OPad-dev/OPad/hardware/pcb/V1/HE/production/aisler/he_input_v1-schematic.pdf

1 | 2 | 3 | 4 | 5 | 6
1 | 2 | 3 | 4 | 5 | 6

AB

C

D

AB

C

### D Date: 2026-10-10

Size: A4 | Rev: V1.1
KiCad E.D.A. 10.0.6 | Id: 1/1

## Title: osuPad Hall Effect Input Module V1

### File: he_input_v1.kicad_sch

### Sheet: /

osuPad

PWR_FLAG

C2
100nF
VCC 1 | OUT | 2 GND 3 | U1 DRV5055A3
VCC 1 | OUT | 2 GND 3 | U2 DRV5055A3

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
J1 MODULE | C3

100nF

TP1

IO6

TP3

IO2 | R1
100k R2
47k | PWR_FLAG

C1

100nF 3V3 3V3

3V3 | 3V3
3V3 GND | GND GND

GND

IN1

IN2 | GND ID ID 3V3 GND

ID
IO6 | 3V3IO2 IO4 | GND

GND

IO4

IO2 IO6

3V3

IN1

IN2 | GND U1/U2 output a ratiometric analog voltage centred on VCC/2; the firmware tracks the peak and applies the rapid-trigger threshold. Module ID: 3V3 x 47k / (100k + 47k) = 1.06 V, read on GPIO8 and decoded as "Hall Effect module V1". Everything is on the bottom side. U1 and U2 sit on the key centres over solid FR-4, with no copper pour in the magnetic path.
J1-6/7/8 are reserved for an SPI variant and are brought out to probe pads TP1..TP3 instead of being left floating. osuPad Hall Effect (Rapid Trigger) input module V1 - two DRV5055 linear Hall sensors Module connector pinout, identical on every osuPad input module: 1 3V3 | 2 GND | 3 IN1 = GPIO10 (ADC1_CH9) | 4 IN2 = GPIO7 (ADC1_CH6) | 5 ID = GPIO8 (ADC1_CH7) | 6 GPIO6 | 7 GPIO4 | 8 GPIO2
