OPad-dev/OPad/osupad_windows_support_plan.md

# osu!pad — Windows Support, Installer and Device Pairing

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

---

## 0. Scope and decisions

### Goal

Ship osu!pad on Windows 10/11 with a real installer, and make the pad and the app feel like **one product** without ever locking the user out of their own hardware.

### Decided (owner, 2026-09-16)

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

### Open decision

- **Version number.** `v1.0.0` is already tagged and published. This plan assumes Windows ships as **`v1.1.0`**; re-cutting a published tag is not recommended. Owner to confirm.

### The one invariant that overrides everything

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

### What "vendor lock, but not really a lock" means here

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

---

## 1. What already works on Windows (verify, don't rewrite)

Confirmed by reading the tree at `0a5c13e`:

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

---

## 2. W0: make the workspace build on Windows (do these first)

Nothing else can be tested until `cargo build --target x86_64-pc-windows-msvc` succeeds.

### W0-1. Abstract the IPC transport

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

---

### W0-2. IPC hardening on Windows (the P2-6 equivalent)

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

---

### W0-3. Single-instance guard for the GUI

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

---

### W0-4. Storage and config paths

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

---

### W0-5. Cross-platform tray

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

---

### W0-6. Resolve the remaining `cfg(target_os = "linux")` sites

**Where.** `desktop/gui/src/main.rs:5, 278, 706, 743, 1008, 1734`

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

---

## 3. W1: Windows platform integration

### W1-1. `platform_windows.rs`

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

---

### W1-2. Hotplug detection

**Problem.** The Linux daemon relies on udev (`packaging/linux/udev/99-osupad.rules`) plus reconnect polling. Windows has no udev.

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

---

### W1-3. Flashing on Windows

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

**Acceptance.** Recovery flash works on Windows with the GUI running, without manually stopping the daemon first.

---

## 4. W2: Installer and uninstaller

### W2-1. Inno Setup script

**Where.** New `packaging/windows/osupad.iss`, plus a build script alongside `scripts/release`.

**Installs:**
- `osupad-gui.exe`, `osupad-daemon.exe`, `osupad-cli.exe` → `%LOCALAPPDATA%\Programs\osupad\`

  Per-user install, not `Program Files`. This avoids requiring admin rights, matches the per-user daemon model, and keeps the uninstall entirely inside the user's own profile.
- Start Menu shortcut for the GUI. **No desktop shortcut by default** — offer it as an unchecked checkbox.
- The `HKCU\...\Run` autostart value from W1-1, as an opt-in checkbox on the final page ("Start osu!pad when I log in", default checked).
- Uninstall entry under `HKCU\Software\Microsoft\Windows\CurrentVersion\Uninstall\osupad`.

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

---

### W2-2. Code signing

Unsigned installers trigger SmartScreen ("Windows protected your PC"), which for a keyboard-adjacent download is a real adoption problem — users are right to be suspicious of unsigned software that installs a keyboard tool at login.

**Options, owner's call:**
- Sign with an OV/EV certificate (~$200-400/yr; EV clears SmartScreen immediately, OV builds reputation over time).
- Ship unsigned and document the SmartScreen bypass in the README.

Not a blocker for a first release; it is a blocker for a comfortable one. Flagging it now so it is a decision, not a surprise.

---

### W2-3. Strong uninstall — no garbage left

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

  > "Also delete your osu!pad settings and lifetime key counters? This cannot be undone."

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

**Acceptance.** Install → use → uninstall (choosing "delete everything") leaves **zero** osu!pad files and **zero** registry values. Verify with a filesystem+registry diff across the whole cycle, and record the procedure in `docs/testing-checklist.md` as a new section. Run the same check for the "keep my data" path and confirm that `%APPDATA%\osupad\` is the *only* thing left.

---

## 5. W3: Device pairing / ownership claim

Cross-platform — this ships on Linux too, not just Windows.

### W3-1. Install identity

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

---

### W3-2. Firmware: owner field in NVS

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

---

### W3-3. Daemon and GUI: the takeover prompt

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

> "This osu!pad is paired with another installation. Its lifetime counters are 1,234,567 / 1,234,567.
> **[Take over and keep the pad's counters]** · [Take over and use this PC's counters] · [Leave it alone]"

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

---

### W3-4. Documented reflash (the nuke path)

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

---

## 6. W4: Verification and release

### W4-1. CI

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

### W4-2. Windows hardware checklist

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

Add a new section for W2-3's install/uninstall filesystem+registry diff.

### W4-3. Latency on Windows

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

### W4-4. Docs

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

---

## 7. Order of work

```
W0-1 ─┬─ W0-2                     (IPC: everything blocks on this)
      └─ W0-3
W0-4, W0-5, W0-6                  (parallel, independent)
   ↓
W1-1, W1-2, W1-3                  (platform integration)
   ↓
W2-1 ─ W2-3                       (installer; W2-2 signing is a side decision)
   ↓
W3-1 → W3-2 → W3-3 → W3-4         (pairing; cross-platform, ships on Linux too)
   ↓
W4-1 … W4-4
```

W3 (pairing) is independent of W0-W2 and could be done first on Linux if Windows stalls. W0-1 blocks every other Windows task and should be the first commit.

---

## 8. Risks

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

---

## 9. Out of scope

- macOS.
- MSIX packaging and Store-style "plug in the pad → Windows offers the app". That needs a Store-signed MSIX; the Inno decision rules it out. The daemon-at-login plus hotplug detection (W1-2) delivers nearly the same feel.
- Any cryptographic enforcement of the pairing model (§0).
- Windows Service hosting for the daemon (W1-1).
- v2 rapid trigger — see `osupad_v2_rapid_trigger_plan.md`.
