OPad-dev/OPad/hardware/pcb/V1/MX/production/mx_input_v1-bottom.png

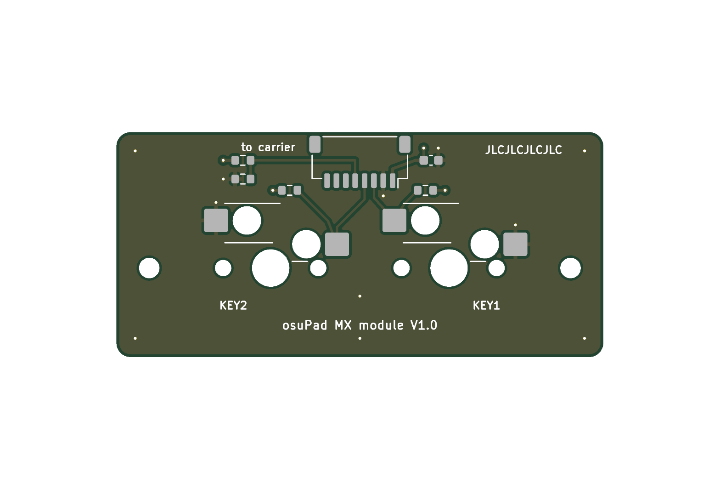
hardware/pcb/V1/MX/production/mx_input_v1-bottom.png
