OPad-dev/OPad/hardware/3d/custom_case/V1.1/tools/waveshare_back.scad

// Parts on the back of the Waveshare ESP32-S3-Touch-LCD-2 taller than 0.8 mm, as
// bounding boxes measured from Waveshare's STEP model (2024-11-08). Deck frame:
// [x0, x1, a0, a1, d0, d1], d = depth behind the glass front. The male headers
// and the four M2 standoffs are included; the model itself is not redistributed.
WS_BACK_BOXES = [
    [10.92, 12.52, 9.43, 12.43, 7.25, 8.35],
    [5.71, 6.53, 9.55, 9.85, 7.22, 8.04],
    [5.72, 6.52, 8.55, 9.55, 7.23, 8.03],
    [5.71, 6.53, 8.25, 8.55, 7.22, 8.04],
    [18.15, 25.20, -4.17, 4.17, 7.20, 10.15],
    [17.79, 18.66, 2.12, 2.39, 7.20, 8.64],
    [17.79, 18.66, -2.39, -2.13, 7.20, 8.64],
    [17.79, 18.66, 1.62, 1.87, 7.20, 8.64],
    [17.79, 18.66, -1.88, -1.63, 7.20, 8.64],
    [17.79, 24.37, 0.12, 0.38, 7.20, 9.22],
    [17.79, 24.37, -0.38, -0.12, 7.20, 9.22],
    [17.79, 24.37, 0.62, 0.88, 7.20, 8.76],
    [17.79, 24.38, -0.88, -0.62, 7.20, 8.76],
    [18.66, 24.37, -0.38, -0.12, 8.52, 8.76],
    [18.66, 24.37, 0.12, 0.38, 8.52, 8.76],
    [17.79, 24.93, -3.43, -2.57, 7.20, 8.78],
    [17.79, 24.58, -1.43, -1.07, 7.20, 9.22],
    [18.66, 24.58, -1.43, -1.07, 8.52, 8.76],
    [17.79, 24.57, 1.07, 1.43, 7.20, 9.22],
    [18.66, 24.58, 1.07, 1.43, 8.52, 8.76],
    [17.79, 24.92, 2.57, 3.43, 7.20, 8.78],
    [20.16, 24.37, 0.63, 0.88, 8.98, 9.22],
    [20.16, 24.38, -0.87, -0.62, 8.98, 9.22],
    [17.79, 24.93, -3.53, -2.41, 7.20, 9.22],
    [17.79, 24.93, 2.41, 3.53, 7.20, 9.22],
    [17.97, 25.50, -4.79, 4.79, 7.20, 10.45],
    [-16.58, -13.58, -5.26, -2.26, 7.20, 8.50],
    [1.15, 3.65, 3.46, 7.96, 7.21, 8.71],
    [1.15, 3.65, 8.09, 12.59, 7.21, 8.71],
    [17.55, 17.85, -12.62, -11.80, 7.22, 8.04],
    [16.55, 17.55, -12.61, -11.81, 7.23, 8.03],
    [16.25, 16.55, -12.62, -11.80, 7.22, 8.04],
    [11.48, 13.78, -11.96, -9.53, 7.20, 8.20],
    [15.18, 18.18, 9.15, 12.15, 7.20, 8.50],
    [-0.72, 2.48, -1.33, 1.32, 7.30, 8.06],
    [1.98, 2.18, 0.92, 1.12, 7.50, 8.08],
    [-8.49, -3.84, 2.85, 3.55, 7.25, 9.50],
    [-8.49, -3.84, -1.55, -0.85, 7.25, 9.50],
    [-8.49, -3.84, -0.45, 0.25, 7.25, 9.50],
    [-8.49, -3.84, -4.85, -4.15, 7.25, 9.50],
    [-8.49, -3.84, -3.75, -3.05, 7.25, 9.50],
    [-8.49, -3.84, -2.65, -1.95, 7.25, 9.50],
    [-8.49, -3.39, 3.78, 4.55, 7.25, 9.50],
    [-8.49, -3.84, 1.75, 2.45, 7.25, 9.50],
    [-8.49, -3.84, 0.65, 1.35, 7.25, 9.50],
    [-7.72, -3.19, 4.70, 5.35, 7.25, 9.20],
    [-8.49, -3.89, -6.05, 5.35, 7.30, 9.67],
    [-8.49, -2.99, -6.05, 5.35, 7.25, 9.90],
    [7.27, 9.57, 9.72, 12.16, 7.20, 8.20],
    [-17.55, 17.97, 13.97, 16.51, 7.20, 15.50],
    [-17.55, 17.97, -16.51, -13.97, 7.20, 15.50],
    [20.38, 24.04, 7.19, 11.75, 7.20, 9.00],
    [20.36, 24.02, -11.73, -7.17, 7.20, 9.00],
    [19.56, 23.06, 12.75, 16.25, 7.20, 9.71],
    [19.56, 23.06, -16.25, -12.75, 7.20, 9.71],
    [-22.64, -19.14, -16.25, -12.75, 7.20, 9.71],
    [-22.64, -19.14, 12.75, 16.25, 7.20, 9.71],
    [1.21, 6.41, -12.92, -5.27, 7.20, 10.60],
    [8.14, 13.83, -8.60, 8.60, 7.20, 9.20],
    [-7.28, -2.11, 6.95, 12.12, 7.20, 9.00],
    [-17.97, -10.27, 3.35, 11.42, 7.20, 8.20],
    [-23.49, -21.49, -8.50, -1.50, 7.20, 8.20]
];
