OPad-dev/OPad/desktop/daemon/src/main.rs

#![cfg_attr(windows, windows_subsystem = "windows")]

use anyhow::{Context, Result};
use parking_lot::Mutex;
use std::collections::HashMap;
use std::sync::atomic::{AtomicBool, Ordering};
use std::sync::Arc;
use std::time::{Duration, Instant};
use tracing::{error, info, warn};
use tracing_subscriber::layer::SubscriberExt;
use tracing_subscriber::util::SubscriberInitExt;

use opad_device::{DeviceEvent, DeviceManager};
use opad_ipc::{create_listener, get_socket_path};
use opad_layout::{Layout, Screen};
use opad_model::{CounterState, DeviceConfig, LogSource, RuntimeMode};
use opad_storage::Storage;
use opad_tosu::{spawn_tosu_supervisor, TosuManager};

pub mod backup;
pub mod device_actor;
pub mod firmware_update;
pub mod identity;
pub mod ipc_handlers;
pub mod log_hub;
pub mod osu_window;
pub mod runtime;
pub mod sync;
pub mod tap_stats;
pub mod telemetry;
pub mod updater;

use device_actor::DeviceCommand;
use log_hub::{LogHub, LogHubLayer};
use runtime::{apply_event, PendingOperations, RuntimeAction, RuntimeController, RuntimeEvent};
use sync::perform_sync;

#[tokio::main]
async fn main() -> Result<()> {
    let log_hub = LogHub::new();
    let fmt_layer = tracing_subscriber::fmt::layer();
    let hub_layer = LogHubLayer::new(log_hub.clone());
    let filter = tracing_subscriber::EnvFilter::from_default_env()
        .add_directive(tracing::Level::INFO.into());

    tracing_subscriber::registry()
        .with(filter)
        .with(fmt_layer)
        .with(hub_layer)
        .init();

    // A panic in any task takes the whole daemon down, loudly, so the service
    // manager (systemd Restart=on-failure) restarts it clean. Left alone, tokio
    // swallows a task's panic and the daemon limps on with that task missing.
    std::panic::set_hook(Box::new(|info| {
        let backtrace = std::backtrace::Backtrace::force_capture();
        error!("opad-daemon panicked: {}\n{}", info, backtrace);
        eprintln!("opad-daemon panicked: {info}");
        std::process::exit(1);
    }));

    info!("Starting opad-daemon v{}", env!("CARGO_PKG_VERSION"));

    let socket_path = get_socket_path();
    if opad_ipc::connect(&socket_path).await.is_ok() {
        anyhow::bail!(
            "Another opad-daemon instance is already running at {}",
            socket_path.display()
        );
    }

    let db_path = opad_model::paths::database_path()
        .context("Cannot resolve where to keep the OPad database")?;
    info!("Using SQLite database at {}", db_path.display());
    let (
        storage,
        storage_error,
        initial_config,
        initial_device,
        initial_counters,
        initial_layouts,
        existing_ids,
    ) = match Storage::open(&db_path) {
        Ok(s) => {
            let cfg = s.load_config().unwrap_or_default();
            let latest = s.load_latest_device_state().unwrap_or(None);
            let mut layouts = HashMap::new();
            for screen in Screen::ALL {
                if let Ok(Some(json)) = s.load_layout(screen.to_wire()) {
                    if let Ok(layout) = Layout::from_json(&json) {
                        layouts.insert(*screen, layout);
                    }
                }
            }
            let (init_dev, init_cnt) = match latest {
                Some((info, counters)) => (Some(info), counters),
                None => (None, CounterState::default()),
            };
            let existing = s
                .list_device_states()
                .unwrap_or_default()
                .into_iter()
                .map(|(info, _)| info.device_id)
                .collect();
            info!("opad-daemon initialized, storage loaded successfully");
            (
                Arc::new(Mutex::new(Some(s))),
                None,
                cfg,
                init_dev,
                init_cnt,
                layouts,
                existing,
            )
        }
        Err(e) => {
            let err_msg = format!("Database error ({}): {}", db_path.display(), e);
            error!(
                "Failed to open/migrate SQLite database: {}. Starting in degraded mode (§P2-12)",
                err_msg
            );
            (
                Arc::new(Mutex::new(None)),
                Some(err_msg),
                DeviceConfig::default(),
                None,
                CounterState::default(),
                HashMap::new(),
                Vec::new(),
            )
        }
    };

    // This install's identity (§W3-1), needed before the first pad connects
    // so an unclaimed pad can be claimed silently on that first HelloAck.
    let install_id = identity::load_or_create(&storage);
    if install_id.is_none() {
        warn!("Running with no install identity; pad ownership will not be recorded (§W3-1)");
    }

    let start_now = Instant::now();
    let mut controller = RuntimeController::new(
        initial_config.clone(),
        initial_device,
        initial_counters,
        initial_layouts,
        storage_error,
        existing_ids,
        start_now,
    );

    controller.set_install_id(install_id.clone());

    // Seed the last-backup time from the directory so a restart reports what
    // is really there rather than "Never".
    match backup::backup_dir() {
        Ok(dir) => {
            controller.state.last_backup = backup::newest(&dir).map(backup::format_stamp);
            info!(
                "Automatic counter backups: {} (keeping the {} most recent, written {:?} after a session settles)",
                dir.display(),
                backup::KEEP,
                runtime::AUTO_BACKUP_DELAY
            );
        }
        Err(e) => warn!("Automatic counter backups are unavailable: {}", e),
    }

    // Tap rate statistics (issue #2): the configured period and its history
    if let Some(s) = storage.lock().as_ref() {
        let tap = &mut controller.state.tap.snapshot;
        match s.tap_history_days() {
            Ok(days) => tap.period_days = days,
            Err(e) => warn!("Cannot read the tap rate history period: {}", e),
        }
        match s.tap_history(tap.period_days, chrono::Utc::now()) {
            Ok(history) => tap.history = Some(history),
            Err(e) => warn!("Cannot read the tap rate history: {}", e),
        }
    }

    let daemon_state = Arc::new(Mutex::new(controller.state.clone()));
    let pending_ops = Arc::new(Mutex::new(PendingOperations::default()));

    // Launch and supervise tosu, then follow its WebSocket
    let tosu_log_path =
        opad_model::paths::tosu_log_path().context("Cannot resolve where to keep the tosu log")?;

    if tosu_log_path.is_file() {
        if let Ok(content) = std::fs::read_to_string(&tosu_log_path) {
            let lines: Vec<&str> = content.lines().collect();
            let start = lines.len().saturating_sub(150);
            for line in &lines[start..] {
                let clean = opad_tosu::strip_ansi(line);
                let trimmed = clean.trim();
                if !trimmed.is_empty() {
                    log_hub.push(
                        LogSource::Tosu,
                        classify_tosu_line(trimmed),
                        "tosu",
                        trimmed,
                    );
                }
            }
        }
    }

    let lh = log_hub.clone();
    let tosu_cb = Arc::new(move |line: &str| {
        let clean = line.trim();
        if !clean.is_empty() {
            lh.push(LogSource::Tosu, classify_tosu_line(clean), "tosu", clean);
        }
    });

    let tosu_supervisor = spawn_tosu_supervisor(
        initial_config.tosu_endpoint.clone(),
        tosu_log_path,
        Some(tosu_cb),
    );
    let (tosu_manager, mut tosu_rx) = TosuManager::new(initial_config.tosu_endpoint.clone());
    let mut tosu_connected_rx = tosu_manager.subscribe_connected();
    let mut tosu_keys_rx = tosu_manager.subscribe_keys();
    tosu_manager.start();
    let mut osu_active_rx = osu_window::watch();

    // Start Device CDC manager
    let (device_manager, mut device_rx) = DeviceManager::new();
    let device_manager = Arc::new(device_manager);
    // Every runtime action reaches the pad through this one ordered queue
    let resend_data = Arc::new(AtomicBool::new(false));
    let device_cmd = device_actor::spawn(device_manager.clone(), resend_data.clone());

    // Setup Local IPC Server
    let socket_path = get_socket_path();
    let ipc_listener = match create_listener(&socket_path) {
        Ok(l) => l,
        Err(opad_ipc::IpcError::AlreadyRunning) => {
            eprintln!("opad-daemon is already running");
            std::process::exit(0);
        }
        Err(e) => return Err(e.into()),
    };

    // Updates: tosu (§U-1) and the app (§U-2). Idle-only, daily, and inert
    // until a signing key is compiled in (§U-0.3).
    let update_service =
        updater::spawn_update_worker(daemon_state.clone(), storage.clone(), tosu_supervisor);

    // Spawn IPC request handling task
    {
        let daemon_state = daemon_state.clone();
        let storage = storage.clone();
        let device_manager = device_manager.clone();
        let log_hub = log_hub.clone();
        let pending_ops = pending_ops.clone();
        let update_service = update_service.clone();

        tokio::spawn(async move {
            loop {
                match ipc_listener.accept().await {
                    Ok(mut stream) => {
                        let daemon_state = daemon_state.clone();
                        let storage = storage.clone();
                        let device_manager = device_manager.clone();
                        let log_hub = log_hub.clone();
                        let pending_ops = pending_ops.clone();
                        let update_service = update_service.clone();

                        tokio::spawn(async move {
                            ipc_handlers::serve_connection(
                                &mut stream,
                                &daemon_state,
                                &storage,
                                &*device_manager,
                                &log_hub,
                                &pending_ops,
                                Some(&update_service),
                            )
                            .await;
                        });
                    }
                    Err(e) => {
                        warn!("IPC accept error: {}", e);
                    }
                }
            }
        });
    }

    // Main Runtime Coordinator loop (§11: IDLE <-> PLAYING <-> COOLDOWN <-> SYNC)
    let mut tick = tokio::time::interval(Duration::from_millis(50));
    let mut last_db_retry = Instant::now();
    let mut last_instant = Instant::now();
    let mut last_system_time = std::time::SystemTime::now();
    // Syncs run in their own task (they can take ~10 s) and report back here
    let (sync_done_tx, mut sync_done_rx) =
        tokio::sync::mpsc::unbounded_channel::<Result<CounterState, String>>();

    loop {
        let mut event_opt = None;

        tokio::select! {
            // 1. Device hardware events
            res = device_rx.recv() => {
                let dev_event = match res {
                    Ok(ev) => ev,
                    Err(tokio::sync::broadcast::error::RecvError::Lagged(skipped)) => {
                        // Whatever was skipped (a Connected, a Counters) is
                        // lost; ask the pad to announce itself again
                        warn!("Fell {} device events behind; re-handshaking with the pad", skipped);
                        device_manager.rehandshake();
                        continue;
                    }
                    Err(tokio::sync::broadcast::error::RecvError::Closed) => {
                        anyhow::bail!("The device event channel closed");
                    }
                };
                match dev_event {
                    DeviceEvent::Connected(info, dev_cfg) => {
                        info!(
                            "ESP32 Device Connected: ID={}, Board={}, Firmware={}, Slot={}",
                            info.device_id,
                            info.board_profile,
                            info.firmware_version,
                            info.running_partition.as_deref().unwrap_or("unknown"),
                        );
                        event_opt = Some(RuntimeEvent::DeviceConnected(info, dev_cfg));
                    }
                    DeviceEvent::Ownership { owner_id } => {
                        event_opt = Some(RuntimeEvent::DeviceOwnership(owner_id));
                    }
                    DeviceEvent::Disconnected => {
                        warn!("ESP32 Device Disconnected");
                        event_opt = Some(RuntimeEvent::DeviceDisconnected);
                    }
                    DeviceEvent::Counters(c) => {
                        event_opt = Some(RuntimeEvent::DeviceCounters(c));
                    }
                    DeviceEvent::StatusUpdate(status) => {
                        event_opt = Some(RuntimeEvent::DeviceLatency(opad_model::LatencyStats {
                            samples: status.latency_samples,
                            p50_us: status.latency_p50_us,
                            p99_us: status.latency_p99_us,
                            p999_us: status.latency_p999_us,
                            max_us: status.latency_max_us,
                            deferred_reports: status.hid_deferred_reports,
                        }));
                    }
                    DeviceEvent::CounterSyncResult { .. } => {}
                    DeviceEvent::ConfigAck { .. } => {}
                    DeviceEvent::LayoutAck { screen, success, message } => {
                        let note = if message.is_empty() { String::new() } else { format!(" ({})", message) };
                        info!(
                            "Layout {} {}{}",
                            Screen::from_wire(screen).map_or("?", |s| s.label()),
                            if success { "applied" } else { "rejected" },
                            note
                        );
                        event_opt = Some(RuntimeEvent::DeviceLayoutAck { screen, success, message });
                    }
                    DeviceEvent::LogBatch(batch) => {
                        event_opt = Some(RuntimeEvent::DeviceLogBatch(batch));
                    }
                    DeviceEvent::PinDetected { .. } | DeviceEvent::BoardTest(_) => {}
                    DeviceEvent::KeyPressTimes(on) => {
                        event_opt = Some(RuntimeEvent::PadPressTimes(on));
                    }
                    DeviceEvent::KeyPresses { now_us, presses, dropped, received } => {
                        event_opt = Some(RuntimeEvent::PadPresses { now_us, presses, dropped, received });
                    }
                }
            }

            // 2. Telemetry events from tosu
            Ok(telemetry) = tosu_rx.recv() => {
                event_opt = Some(RuntimeEvent::TosuTelemetry {
                    is_playing: telemetry.is_playing,
                    live_time_ms: telemetry.live_time_ms,
                    title: telemetry.title,
                    values: telemetry.values,
                    beatmap: telemetry.beatmap,
                    failed: telemetry.failed,
                    clock: telemetry.clock,
                    other_player: telemetry.other_player,
                });
            }

            // 2b. osu!'s key counters, for the tap rate (issue #2). A lag
            //     loses a few presses from one attempt's statistics, nothing
            //     more, so it is not worth resynchronising anything for.
            res = tosu_keys_rx.recv() => {
                match res {
                    Ok(keys) => event_opt = Some(RuntimeEvent::TosuKeys(keys)),
                    Err(tokio::sync::broadcast::error::RecvError::Lagged(n)) => {
                        warn!("Fell {} tosu key updates behind; the tap rate skips them", n);
                    }
                    Err(tokio::sync::broadcast::error::RecvError::Closed) => {}
                }
            }

            // 3. tosu WebSocket connected / disconnected
            Ok(()) = tosu_connected_rx.changed() => {
                let connected = *tosu_connected_rx.borrow_and_update();
                info!("{}", if connected { "tosu connected" } else { "tosu disconnected" });
                event_opt = Some(RuntimeEvent::TosuConnectionChanged(connected));
            }

            // 3b. osu! came to the front / started, or went away: where the
            //     pad's volume swipes go
            Ok(()) = osu_active_rx.changed() => {
                let active = *osu_active_rx.borrow_and_update();
                info!("{}", if active { "osu! active: volume swipes go to osu!" } else { "osu! inactive: volume swipes set the system volume" });
                event_opt = Some(RuntimeEvent::OsuActiveChanged(active));
            }

            // 4. A background sync finished
            Some(res) = sync_done_rx.recv() => {
                event_opt = Some(match res {
                    Ok(counters) => RuntimeEvent::SyncCompleted {
                        success: true,
                        counters,
                        time_str: Some(chrono::Utc::now().to_rfc3339()),
                        error: None,
                    },
                    Err(e) => RuntimeEvent::SyncCompleted {
                        success: false,
                        // Unchanged by the failed sync; the shared state, not
                        // the controller's copy from the previous event
                        counters: daemon_state.lock().counters.clone(),
                        time_str: None,
                        error: Some(e),
                    },
                });
            }

            // 5. Periodic tick
            _ = tick.tick() => {
                let now = Instant::now();

                // Periodic clock jump check
                let now_system = std::time::SystemTime::now();
                let elapsed_instant = now.saturating_duration_since(last_instant);
                let clock_jump = match now_system.duration_since(last_system_time) {
                    Ok(sys_elapsed) => sys_elapsed.abs_diff(elapsed_instant) > Duration::from_secs(2),
                    Err(_) => true,
                };
                last_instant = now;
                last_system_time = now_system;

                if clock_jump && {
                    let ds = daemon_state.lock();
                    ds.device_connected && ds.mode == RuntimeMode::Idle
                } {
                    let _ = device_cmd.send(DeviceCommand::TimeSync).await;
                }

                // A telemetry diff met a full device queue, or a message to
                // the pad was lost on the wire: resend everything, or the
                // song, stars, ... stay missing until they next change
                let lost = device_manager.take_lost_writes();
                if resend_data.swap(false, Ordering::SeqCst) || lost {
                    controller.data_sync.reset_sent();
                }

                // Retry opening SQLite every 60s if unavailable (§P2-12)
                if storage.lock().is_none() && last_db_retry.elapsed() >= Duration::from_secs(60) {
                    last_db_retry = Instant::now();
                    info!("Retrying SQLite database connection at {}", db_path.display());
                    match Storage::open(&db_path) {
                        Ok(s) => {
                            info!("Successfully reconnected to SQLite database at {}", db_path.display());
                            let cfg = s.load_config().ok();
                            let mut layouts = Vec::new();
                            for screen in Screen::ALL {
                                if let Ok(Some(json)) = s.load_layout(screen.to_wire()) {
                                    if let Ok(l) = Layout::from_json(&json) {
                                        layouts.push((*screen, l));
                                    }
                                }
                            }
                            let device_id = daemon_state.lock().device_info.as_ref().map(|i| i.device_id.clone());
                            let stored_dev = if let Some(device_id) = &device_id {
                                s.load_device_state(device_id).unwrap_or(None)
                            } else {
                                None
                            };
                            *storage.lock() = Some(s);
                            let _ = apply_event(&mut controller, &daemon_state, &pending_ops, RuntimeEvent::SqliteReconnected {
                                config: cfg,
                                layouts,
                                stored_device: stored_dev,
                            }, now);
                        }
                        Err(e) => {
                            warn!("SQLite database reconnection attempt failed: {}", e);
                            let _ = apply_event(&mut controller, &daemon_state, &pending_ops, RuntimeEvent::SqliteError(format!("Database error ({}): {}", db_path.display(), e)), now);
                        }
                    }
                }

                event_opt = Some(RuntimeEvent::Tick(now));
            }
        }

        if let Some(event) = event_opt {
            let now = Instant::now();
            let actions = apply_event(&mut controller, &daemon_state, &pending_ops, event, now);

            for action in actions {
                match action {
                    RuntimeAction::SendTimeSync => {
                        let _ = device_cmd.send(DeviceCommand::TimeSync).await;
                    }
                    RuntimeAction::ClaimOwnership => {
                        // §W3-2: an NVS write, which the firmware honours only
                        // in IDLE. Connect time already is one.
                        if let Some(owner) =
                            install_id.as_deref().and_then(identity::parse_owner_id)
                        {
                            let _ = device_cmd
                                .send(DeviceCommand::ClaimOwnership(owner.to_vec()))
                                .await;
                        }
                    }
                    RuntimeAction::SendConfig(cfg) => {
                        let _ = device_cmd.send(DeviceCommand::Config(cfg)).await;
                    }
                    RuntimeAction::SaveDeviceConfig(cfg) => {
                        let s_guard = storage.lock();
                        if let Some(s) = s_guard.as_ref() {
                            if let Err(e) = s.save_config(&cfg) {
                                warn!("Failed to persist device configuration from pad: {}", e);
                            } else {
                                info!("Saved pad configuration to SQLite database");
                            }
                        }
                    }
                    RuntimeAction::SendHostStatus {
                        tosu_connected,
                        is_playing,
                        play_id,
                        osu_active,
                    } => {
                        let _ = device_cmd
                            .send(DeviceCommand::HostStatus {
                                tosu_connected,
                                is_playing,
                                play_id,
                                osu_active,
                            })
                            .await;
                    }
                    RuntimeAction::SendDataUpdate(changes) => {
                        let _ = device_cmd.send(DeviceCommand::DataUpdate(changes)).await;
                    }
                    RuntimeAction::SendLayout(screen, layout) => {
                        let _ = device_cmd.send(DeviceCommand::Layout(screen, layout)).await;
                    }
                    RuntimeAction::TakeOverIfPadIsAhead => {
                        let ds = daemon_state.clone();
                        let stg = storage.clone();
                        let dm = device_manager.clone();
                        let hub = log_hub.clone();
                        let po = pending_ops.clone();
                        tokio::spawn(async move {
                            ipc_handlers::take_over_if_pad_is_ahead(&ds, &stg, &*dm, &hub, &po)
                                .await;
                        });
                    }
                    RuntimeAction::TriggerSync => {
                        let ds = daemon_state.clone();
                        let stg = storage.clone();
                        let dm = device_manager.clone();
                        let po = pending_ops.clone();
                        let done = sync_done_tx.clone();
                        tokio::spawn(async move {
                            let res = perform_sync(&ds, &stg, &*dm, &po).await;
                            let _ = done.send(res);
                        });
                    }
                    RuntimeAction::RequestDeviceStatus => {
                        let _ = device_cmd.send(DeviceCommand::RequestStatus).await;
                    }
                    RuntimeAction::SetStorageWritesAllowed(allowed) => {
                        if let Some(s) = storage.lock().as_mut() {
                            s.set_writes_allowed(allowed);
                        }
                    }
                    RuntimeAction::SaveInitialDeviceState(info, counters) => {
                        if let Some(s) = storage.lock().as_ref() {
                            let _ = s.save_device_state(&info, &counters);
                        }
                    }
                    RuntimeAction::TouchDeviceLastSeen(device_id) => {
                        if let Some(s) = storage.lock().as_ref() {
                            let _ = s.touch_device_last_seen(&device_id);
                        }
                    }
                    RuntimeAction::PushEspLog {
                        level,
                        tag,
                        message,
                    } => {
                        log_hub.push(LogSource::Esp, level, &tag, message);
                    }
                    RuntimeAction::SaveTapStats {
                        attempts,
                        period_days,
                    } => {
                        // IDLE by construction. A failure keeps the attempts
                        // queued for the next IDLE tick rather than losing them.
                        let (unsaved, period_saved) = match storage.lock().as_ref() {
                            None => (Some(attempts), period_days.is_none()),
                            Some(s) => {
                                let unsaved = match s.save_tap_attempts(&attempts) {
                                    Ok(n) => {
                                        if n > 0 {
                                            info!("Saved the tap rate of {} attempts", n);
                                        }
                                        None
                                    }
                                    Err(e) => {
                                        warn!(
                                            "Cannot save the tap rate of {} attempts yet: {}",
                                            attempts.len(),
                                            e
                                        );
                                        Some(attempts)
                                    }
                                };
                                let period_saved = period_days.is_none_or(|days| {
                                    s.set_tap_history_days(days)
                                        .map_err(|e| {
                                            warn!(
                                                "Cannot save the tap rate history period yet: {}",
                                                e
                                            )
                                        })
                                        .is_ok()
                                });
                                (unsaved, period_saved)
                            }
                        };
                        if let Some(attempts) = unsaved {
                            controller.requeue_tap_attempts(attempts);
                        }
                        if !period_saved {
                            daemon_state.lock().tap.period_unsaved = true;
                        }
                        tap_stats::refresh_history(&storage, &daemon_state);
                    }
                    RuntimeAction::RefreshTapHistory => {
                        tap_stats::refresh_history(&storage, &daemon_state);
                    }
                    RuntimeAction::WriteAutoBackup => {
                        // Synchronous and cheap (one small JSON file), and we
                        // are in IDLE by construction. Every failure inside is
                        // logged and swallowed: a backup must never be able to
                        // take the daemon down or hold up anything else.
                        if let Some(backup) = backup::current(&daemon_state, &storage) {
                            if let Some(at) = backup::write_and_log(&backup) {
                                daemon_state.lock().last_backup = Some(backup::format_stamp(at));
                            }
                        }
                    }
                }
            }
        }
    }
}

/// Level of a tosu output line (ANSI already stripped), from its wording
fn classify_tosu_line(line: &str) -> opad_model::LogLevel {
    if line.contains("error") || line.contains("Error") {
        opad_model::LogLevel::Error
    } else if line.contains("warn") || line.contains("Warn") {
        opad_model::LogLevel::Warn
    } else {
        opad_model::LogLevel::Info
    }
}

#[cfg(test)]
mod tests {
    use super::*;

    #[test]
    fn tosu_lines_are_classified_by_their_wording() {
        use opad_model::LogLevel;
        assert_eq!(
            classify_tosu_line("[tosu] Error: port in use"),
            LogLevel::Error
        );
        assert_eq!(classify_tosu_line("socket error"), LogLevel::Error);
        assert_eq!(classify_tosu_line("Warn: slow memory read"), LogLevel::Warn);
        assert_eq!(classify_tosu_line("Server started"), LogLevel::Info);
    }

    use crate::ipc_handlers::handle_ipc_request;
    use crate::runtime::DaemonState;
    use opad_ipc::{IpcRequest, IpcResponse};
    use opad_model::{CounterSource, DeviceInfo};

    #[tokio::test]
    async fn test_sqlite_failure_isolation() {
        let (device_manager, _) = DeviceManager::new_dummy();
        let device_manager = Arc::new(device_manager);
        let log_hub = LogHub::new();
        let pending_ops = Arc::new(Mutex::new(PendingOperations::default()));
        let storage: Arc<Mutex<Option<Storage>>> = Arc::new(Mutex::new(None));

        let daemon_state = Arc::new(Mutex::new(DaemonState {
            mode: RuntimeMode::Idle,
            device_connected: true,
            device_info: Some(DeviceInfo {
                device_id: "OSUPAD-TEST".to_string(),
                board_profile: "waveshare_esp32s3_touch_lcd_2".to_string(),
                firmware_version: "1.0.0".to_string(),
                protocol_version: 1,
                running_partition: None,
            }),
            counters: CounterState {
                device_id: "OSUPAD-TEST".to_string(),
                counter_generation: 1,
                lifetime_key1: 50,
                lifetime_key2: 60,
                map_key1: 0,
                map_key2: 0,
            },
            counters_source: CounterSource::Device,
            pc_counters: None,
            esp_counters: Some(CounterState {
                device_id: "OSUPAD-TEST".to_string(),
                counter_generation: 1,
                lifetime_key1: 50,
                lifetime_key2: 60,
                map_key1: 0,
                map_key2: 0,
            }),
            config: DeviceConfig::default(),
            last_sync_time: None,
            last_sync_error: None,
            storage_error: Some("Database permission denied".to_string()),
            tosu_connected: false,
            osu_active: false,
            latency: None,
            pending_replacement: None,
            install_id: None,
            pending_takeover: None,
            foreign_pad: false,
            nvs_restore_pending: false,
            tap: Default::default(),
            incompatible: None,
            ui_values: Vec::new(),
            custom_layouts: HashMap::new(),
            last_backup: None,
        }));

        // 1. GetStatus surfaces storage_error
        let resp = handle_ipc_request(
            IpcRequest::GetStatus,
            &daemon_state,
            &storage,
            &*device_manager,
            &log_hub,
            &pending_ops,
            None,
        )
        .await;
        match resp {
            IpcResponse::Status { storage_error, .. } => {
                assert_eq!(
                    storage_error,
                    Some("Database permission denied".to_string())
                );
            }
            other => panic!("Expected Status response, got {:?}", other),
        }

        // 2. Destructive/reconciliation operations rejected without SQLite
        let resp = handle_ipc_request(
            IpcRequest::ForceSync,
            &daemon_state,
            &storage,
            &*device_manager,
            &log_hub,
            &pending_ops,
            None,
        )
        .await;
        assert!(matches!(resp, IpcResponse::OperationRejected { .. }));

        let resp = handle_ipc_request(
            IpcRequest::ResetCounters { confirm: true },
            &daemon_state,
            &storage,
            &*device_manager,
            &log_hub,
            &pending_ops,
            None,
        )
        .await;
        assert!(matches!(resp, IpcResponse::OperationRejected { .. }));

        let resp = handle_ipc_request(
            IpcRequest::RestoreDeviceFromPc { confirm: true },
            &daemon_state,
            &storage,
            &*device_manager,
            &log_hub,
            &pending_ops,
            None,
        )
        .await;
        assert!(matches!(resp, IpcResponse::OperationRejected { .. }));

        let resp = handle_ipc_request(
            IpcRequest::ImportPcFromDevice { confirm: true },
            &daemon_state,
            &storage,
            &*device_manager,
            &log_hub,
            &pending_ops,
            None,
        )
        .await;
        assert!(matches!(resp, IpcResponse::OperationRejected { .. }));

        // 3. Layouts still work in-memory
        let resp = handle_ipc_request(
            IpcRequest::GetLayouts,
            &daemon_state,
            &storage,
            &*device_manager,
            &log_hub,
            &pending_ops,
            None,
        )
        .await;
        assert!(matches!(
            resp,
            IpcResponse::Layouts {
                idle: None,
                playing: None
            }
        ));

        // 4. perform_sync does not modify ESP counters when storage is None
        let res = perform_sync(&daemon_state, &storage, &*device_manager, &pending_ops).await;
        assert!(res.is_err());
        let st = daemon_state.lock();
        assert_eq!(st.counters.lifetime_key1, 50);
        assert_eq!(st.counters.lifetime_key2, 60);
        assert!(st.last_sync_error.is_some());
    }
}
