OPad-dev/OPad/firmware/main/input/keypad.c

#include "keypad.h"
#include "debounce.h"
#include "boards/waveshare_esp32s3_touch_lcd_2/board.h"
#include "ui/ui.h"
#include "usb/usb_hid.h"
#include "freertos/FreeRTOS.h"
#include "freertos/task.h"
#include "esp_timer.h"
#include "esp_log.h"
#include <stdatomic.h>
#include "input/latency_stats.h"
#include "input/press_log.h"
#include "driver/gpio.h"
#include "esp_rom_sys.h"
#include "diag/diag.h"
#include "config/device_config.h"

static const char *TAG = "keypad";

static portMUX_TYPE s_keypad_spinlock = portMUX_INITIALIZER_UNLOCKED;
static debounce_state_t s_key_debounce[KEY_ID_COUNT];

#define KEYPAD_DEFAULT_KEY1_GPIO 14
#define KEYPAD_DEFAULT_KEY2_GPIO 9

static keypad_config_t s_config = {
    .keycode1 = 0x1D,       // 'z'
    .keycode2 = 0x1B,       // 'x'
    .debounce_us = DEBOUNCE_DEFAULT_US,
    .key1_gpio = KEYPAD_DEFAULT_KEY1_GPIO,
    .key2_gpio = KEYPAD_DEFAULT_KEY2_GPIO,
};

static keypad_config_t s_staged_config;
static volatile bool s_config_staged = false;

// Pin detection requests, served by the keypad task (the one task that may
// touch key GPIOs). Guarded by s_keypad_spinlock.
static uint32_t s_detect_req_id = 0;
static uint32_t s_detect_req_timeout_ms;
static uint32_t s_detect_req_exclude;
static uint32_t s_detect_done_id = 0;
static int s_detect_done_pin = -1;

// Key line test requests (keypad_line_test), also served by the keypad task.
// Guarded by s_keypad_spinlock.
static uint32_t s_line_test_req_id = 0;
static uint32_t s_line_test_done_id = 0;
static keypad_line_test_t s_line_test_result;

static volatile bool s_key_state[KEY_ID_COUNT] = {false, false};
static volatile int64_t s_last_transition_us[KEY_ID_COUNT] = {0, 0};
static atomic_llong s_key1_last_press_us = 0;
static atomic_llong s_key2_last_press_us = 0;

static atomic_uint_least64_t s_key1_lifetime_presses = 0;
static atomic_uint_least64_t s_key2_lifetime_presses = 0;
// Presses in the current osu! attempt; zeroed by the host on every new play
static atomic_uint_least32_t s_key1_map_presses = 0;
static atomic_uint_least32_t s_key2_map_presses = 0;

static TaskHandle_t s_input_task_handle = NULL;
// Off when the input module is one v1 cannot read (Hall Effect): its analog
// outputs on the key pins would otherwise register as presses
static volatile bool s_input_enabled = true;
static keypad_state_callback_t s_callback = NULL;

static void IRAM_ATTR gpio_isr_handler(void *arg)
{
    int key_index = (intptr_t)arg - 1;
    if (key_index < 0 || key_index >= KEY_ID_COUNT || !s_input_enabled) {
        return;
    }

    int64_t now = esp_timer_get_time();
    bool current_pressed = (key_index == 0) ? board_key1_read() : board_key2_read();

    portENTER_CRITICAL_ISR(&s_keypad_spinlock);
    debounce_action_t action = debounce_step(
        &s_key_debounce[key_index],
        now,
        current_pressed,
        DEBOUNCE_SOURCE_EDGE,
        s_config.debounce_us
    );

    if (action != DEBOUNCE_ACTION_NONE) {
        s_key_state[key_index] = s_key_debounce[key_index].accepted_pressed;
        s_last_transition_us[key_index] = s_key_debounce[key_index].last_transition_us;

        // Counting rule: only accepted press transitions increment counters.
        if (action == DEBOUNCE_ACTION_PRESS) {
            if (key_index == 0) {
                atomic_fetch_add_explicit(&s_key1_lifetime_presses, 1, memory_order_relaxed);
                atomic_fetch_add_explicit(&s_key1_map_presses, 1, memory_order_relaxed);
                atomic_store_explicit(&s_key1_last_press_us, now, memory_order_relaxed);
                press_log_push(1, now);
            } else {
                atomic_fetch_add_explicit(&s_key2_lifetime_presses, 1, memory_order_relaxed);
                atomic_fetch_add_explicit(&s_key2_map_presses, 1, memory_order_relaxed);
                atomic_store_explicit(&s_key2_last_press_us, now, memory_order_relaxed);
                press_log_push(2, now);
            }
        }

        BaseType_t high_task_wakeup = pdFALSE;
        if (s_input_task_handle != NULL) {
            vTaskNotifyGiveFromISR(s_input_task_handle, &high_task_wakeup);
            if (high_task_wakeup) {
                portYIELD_FROM_ISR();
            }
        }
    }
    portEXIT_CRITICAL_ISR(&s_keypad_spinlock);
}

// Pin level as a pressed state, or released while input is off: an HE module's
// analog outputs read as pressed and would hold a key down forever
static bool read_key_level(int key_index)
{
    if (!s_input_enabled) {
        return false;
    }
    return key_index == 0 ? board_key1_read() : board_key2_read();
}

// Start debouncing again from the pins as they read now. True if a key reads
// pressed, so the caller can have the keypad task report it.
static bool restart_debounce_from_pins(void)
{
    bool levels[KEY_ID_COUNT] = {read_key_level(0), read_key_level(1)};
    portENTER_CRITICAL(&s_keypad_spinlock);
    for (int i = 0; i < KEY_ID_COUNT; i++) {
        debounce_init(&s_key_debounce[i], levels[i]);
        s_key_state[i] = levels[i];
        s_last_transition_us[i] = esp_timer_get_time();
    }
    portEXIT_CRITICAL(&s_keypad_spinlock);
    return levels[0] || levels[1];
}

// How long a key line gets to settle after its pull changes. The pin, carrier
// trace and cable are tens of pF against a ~45k internal pull: microseconds.
#define LINE_TEST_SETTLE_US 300

/*
 * Swap each key pin's internal pull-up for a pull-down and read it. A line
 * that still reads high has an external pull-up: the MX module's 10k (R1/R2),
 * which proves the cable, the carrier trace and both connectors carry it. A
 * line low even with the pull-up is a held switch or a short to GND.
 *
 * Runs on the keypad task, about 1 ms. Edges are ignored meanwhile (no HID
 * report is sent in between, the task is busy here) and debouncing restarts
 * from the pins afterwards, so a key held through the test stays held.
 */
static void line_test_run(keypad_line_test_t *r)
{
    portENTER_CRITICAL(&s_keypad_spinlock);
    keypad_config_t cfg = s_config;
    portEXIT_CRITICAL(&s_keypad_spinlock);

    gpio_num_t pins[KEY_ID_COUNT] = {(gpio_num_t)cfg.key1_gpio, (gpio_num_t)cfg.key2_gpio};
    *r = (keypad_line_test_t){
        .gpio = {cfg.key1_gpio, cfg.key2_gpio},
    };
    if (!s_input_enabled) {
        return; // Hall Effect outputs on the pins: nothing a pull test can say
    }

    s_input_enabled = false;
    for (int i = 0; i < KEY_ID_COUNT; i++) {
        r->high_with_pullup[i] = gpio_get_level(pins[i]) != 0;
        gpio_set_pull_mode(pins[i], GPIO_PULLDOWN_ONLY);
    }
    esp_rom_delay_us(LINE_TEST_SETTLE_US);
    for (int i = 0; i < KEY_ID_COUNT; i++) {
        r->high_with_pulldown[i] = gpio_get_level(pins[i]) != 0;
        gpio_set_pull_mode(pins[i], GPIO_PULLUP_ONLY);
    }
    esp_rom_delay_us(LINE_TEST_SETTLE_US);
    s_input_enabled = true;
    restart_debounce_from_pins();
    r->ran = true;
}

static void line_test_step(void)
{
    portENTER_CRITICAL(&s_keypad_spinlock);
    uint32_t req_id = s_line_test_req_id;
    bool pending = req_id != s_line_test_done_id;
    portEXIT_CRITICAL(&s_keypad_spinlock);
    if (!pending) {
        return;
    }
    keypad_line_test_t result;
    line_test_run(&result);
    portENTER_CRITICAL(&s_keypad_spinlock);
    s_line_test_result = result;
    s_line_test_done_id = req_id;
    portEXIT_CRITICAL(&s_keypad_spinlock);
    // Report whatever the pins read now (a key pressed during the test)
    xTaskNotifyGive(s_input_task_handle);
}

#define DETECT_POLL_TICKS (pdMS_TO_TICKS(10) ? pdMS_TO_TICKS(10) : 1)
// A pin must read LOW this long to count as pressed
#define DETECT_CONFIRM_US 15000

// A pin scan in progress. Stepped by the keypad task between key events, so
// key reports keep flowing and the protocol task is never blocked by it.
typedef struct {
    bool active;
    uint32_t id;
    uint32_t exclude;
    uint64_t pin_mask;     // pins this scan configured, released when it ends
    int64_t deadline_us;
    int candidate;         // pin seen LOW, waiting for it to stay LOW
    int64_t candidate_since_us;
} detect_scan_t;

static void detect_scan_release(const detect_scan_t *scan)
{
    // The key pins may have moved onto a scanned pin meanwhile: leave those armed
    portENTER_CRITICAL(&s_keypad_spinlock);
    keypad_config_t cfg = s_config;
    portEXIT_CRITICAL(&s_keypad_spinlock);
    for (size_t i = 0; i < KEY_GPIO_ALLOWED_COUNT; i++) {
        uint8_t pin = KEY_GPIO_ALLOWED[i];
        if ((scan->pin_mask & (1ULL << pin)) && pin != cfg.key1_gpio && pin != cfg.key2_gpio) {
            gpio_reset_pin(pin);
        }
    }
}

static void detect_scan_step(detect_scan_t *scan)
{
    portENTER_CRITICAL(&s_keypad_spinlock);
    uint32_t req_id = s_detect_req_id;
    uint32_t timeout_ms = s_detect_req_timeout_ms;
    uint32_t exclude = s_detect_req_exclude;
    keypad_config_t cfg = s_config;
    portEXIT_CRITICAL(&s_keypad_spinlock);

    if (req_id != scan->id) {
        // A new request replaces the running scan, which gets no result
        if (scan->active) {
            detect_scan_release(scan);
        }
        ESP_LOGI(TAG, "Starting interactive pin detection (timeout=%lu ms, exclude=GPIO%lu)",
                 (unsigned long)timeout_ms, (unsigned long)exclude);
        // Configure candidate pins with internal pull-ups. The active key pins are
        // already pulled-up inputs, so they are scanned as they are: reconfiguring
        // them here would turn their interrupts off mid-session.
        uint64_t pin_mask = 0;
        for (size_t i = 0; i < KEY_GPIO_ALLOWED_COUNT; i++) {
            uint8_t pin = KEY_GPIO_ALLOWED[i];
            if (device_config_key_gpio_supported(pin) &&
                pin != exclude && pin != cfg.key1_gpio && pin != cfg.key2_gpio) {
                pin_mask |= (1ULL << pin);
            }
        }
        gpio_config_t io_conf = {
            .pin_bit_mask = pin_mask,
            .mode = GPIO_MODE_INPUT,
            .pull_up_en = GPIO_PULLUP_ENABLE,
            .pull_down_en = GPIO_PULLDOWN_DISABLE,
            .intr_type = GPIO_INTR_DISABLE,
        };
        gpio_config(&io_conf);
        esp_rom_delay_us(500);

        *scan = (detect_scan_t){
            .active = true,
            .id = req_id,
            .exclude = exclude,
            .pin_mask = pin_mask,
            .deadline_us = esp_timer_get_time() + (int64_t)timeout_ms * 1000,
            .candidate = -1,
        };
    }
    if (!scan->active) {
        return;
    }

    int64_t now = esp_timer_get_time();
    int detected_pin = -1;
    if (scan->candidate >= 0) {
        if (gpio_get_level(scan->candidate) != 0) {
            scan->candidate = -1;
        } else if (now - scan->candidate_since_us >= DETECT_CONFIRM_US) {
            detected_pin = scan->candidate;
            ESP_LOGI(TAG, "Pin detected: GPIO%d pulled LOW", detected_pin);
        }
    }
    if (scan->candidate < 0) {
        for (size_t i = 0; i < KEY_GPIO_ALLOWED_COUNT; i++) {
            uint8_t pin = KEY_GPIO_ALLOWED[i];
            if (device_config_key_gpio_supported(pin) && pin != scan->exclude &&
                gpio_get_level(pin) == 0) {
                scan->candidate = pin;
                scan->candidate_since_us = now;
                break;
            }
        }
    }

    if (detected_pin < 0 && now < scan->deadline_us) {
        return;
    }
    detect_scan_release(scan);
    scan->active = false;
    portENTER_CRITICAL(&s_keypad_spinlock);
    s_detect_done_id = scan->id;
    s_detect_done_pin = detected_pin;
    portEXIT_CRITICAL(&s_keypad_spinlock);
}

static void keypad_task(void *pvParameters)
{
    (void)pvParameters;
    ESP_LOGI(TAG, "Keypad high-priority processing task started on core %d", xPortGetCoreID());

    bool reported_state[KEY_ID_COUNT] = {false, false};
    detect_scan_t scan = {0};

    while (1) {
        // Calculate wait timeout based on smallest remaining lockout
        int64_t now_us = esp_timer_get_time();
        TickType_t wait_ticks = portMAX_DELAY;
        int64_t min_rem_us = -1;

        portENTER_CRITICAL(&s_keypad_spinlock);
        for (int i = 0; i < KEY_ID_COUNT; i++) {
            if (!s_key_debounce[i].resampled && s_key_debounce[i].lockout_end_us > 0) {
                int64_t rem = s_key_debounce[i].lockout_end_us - now_us;
                if (rem <= 0) {
                    min_rem_us = 0;
                    break;
                }
                if (min_rem_us < 0 || rem < min_rem_us) {
                    min_rem_us = rem;
                }
            }
        }
        portEXIT_CRITICAL(&s_keypad_spinlock);

        if (min_rem_us >= 0) {
            if (min_rem_us == 0) {
                wait_ticks = 0;
            } else {
                uint32_t ms = (uint32_t)((min_rem_us + 999) / 1000);
                wait_ticks = pdMS_TO_TICKS(ms);
                if (wait_ticks == 0) {
                    wait_ticks = 1;
                }
            }
        }

        if (scan.active && (wait_ticks == portMAX_DELAY || wait_ticks > DETECT_POLL_TICKS)) {
            wait_ticks = DETECT_POLL_TICKS;
        }

        ulTaskNotifyTake(pdTRUE, wait_ticks);

        now_us = esp_timer_get_time();

        // 1. Re-sample keys whose lockout has expired
        for (int i = 0; i < KEY_ID_COUNT; i++) {
            bool need_resample = false;
            portENTER_CRITICAL(&s_keypad_spinlock);
            if (!s_key_debounce[i].resampled && s_key_debounce[i].lockout_end_us > 0 &&
                now_us >= s_key_debounce[i].lockout_end_us) {
                need_resample = true;
            }
            portEXIT_CRITICAL(&s_keypad_spinlock);

            if (need_resample && !s_input_enabled) {
                // An edge that slipped in as input was turned off: forget it
                portENTER_CRITICAL(&s_keypad_spinlock);
                debounce_init(&s_key_debounce[i], false);
                s_key_state[i] = false;
                portEXIT_CRITICAL(&s_keypad_spinlock);
            } else if (need_resample) {
                bool pin_level = (i == 0) ? board_key1_read() : board_key2_read();
                portENTER_CRITICAL(&s_keypad_spinlock);
                debounce_action_t action = debounce_step(
                    &s_key_debounce[i],
                    now_us,
                    pin_level,
                    DEBOUNCE_SOURCE_RESAMPLE,
                    s_config.debounce_us
                );

                if (action != DEBOUNCE_ACTION_NONE) {
                    s_key_state[i] = s_key_debounce[i].accepted_pressed;
                    s_last_transition_us[i] = s_key_debounce[i].last_transition_us;

                    // Counting rule: only accepted press transitions increment counters,
                    // including presses applied by resample. A glitch press that is later
                    // corrected will have been counted once; that is acceptable.
                    if (action == DEBOUNCE_ACTION_PRESS) {
                        if (i == 0) {
                            atomic_fetch_add_explicit(&s_key1_lifetime_presses, 1, memory_order_relaxed);
                            atomic_fetch_add_explicit(&s_key1_map_presses, 1, memory_order_relaxed);
                            atomic_store_explicit(&s_key1_last_press_us, now_us, memory_order_relaxed);
                            // Confirmed by the resample, so up to one lockout
                            // (debounce_us) after the edge it missed
                            press_log_push(1, now_us);
                        } else {
                            atomic_fetch_add_explicit(&s_key2_lifetime_presses, 1, memory_order_relaxed);
                            atomic_fetch_add_explicit(&s_key2_map_presses, 1, memory_order_relaxed);
                            atomic_store_explicit(&s_key2_last_press_us, now_us, memory_order_relaxed);
                            press_log_push(2, now_us);
                        }
                    }
                }
                portEXIT_CRITICAL(&s_keypad_spinlock);
            }
        }

        // 2. Submit state changes to USB HID
        for (int i = 0; i < KEY_ID_COUNT; i++) {
            bool current;
            int64_t edge_us;

            portENTER_CRITICAL(&s_keypad_spinlock);
            // Input off: report released whatever the pin reads (sends one
            // release if a key was down)
            current = s_input_enabled && s_key_state[i];
            edge_us = s_last_transition_us[i];
            portEXIT_CRITICAL(&s_keypad_spinlock);

            if (current != reported_state[i]) {
                reported_state[i] = current;
                // HID report first; activity bookkeeping only after it is submitted
                if (s_callback) {
                    if (s_callback(i, current, edge_us)) {
                        latency_stats_record((uint32_t)(esp_timer_get_time() - edge_us));
                    } else {
                        // Resent by the HID layer, which records the latency then
                        latency_stats_record_deferred();
                    }
                }
#if defined(CONFIG_OSUPAD_BENCH_DEBUG_GPIO) || defined(OSUPAD_BENCH_DEBUG_GPIO)
                gpio_set_level(CONFIG_OSUPAD_BENCH_DEBUG_GPIO_NUM, current ? 1 : 0);
#endif
                if (current) {
                    ui_notify_activity();
                }
            }
        }

        // 3. If both keys are currently released, apply any staged config change
        bool move_pins = false;
        keypad_config_t applied;
        keypad_config_t previous;
        portENTER_CRITICAL(&s_keypad_spinlock);
        if (s_config_staged && !s_key_state[0] && !s_key_state[1] &&
            !reported_state[0] && !reported_state[1]) {
            move_pins = s_staged_config.key1_gpio != s_config.key1_gpio ||
                        s_staged_config.key2_gpio != s_config.key2_gpio;
            applied = s_staged_config;
            previous = s_config;
            if (!move_pins) {
                s_config = applied;
                usb_hid_set_keycodes(applied.keycode1, applied.keycode2);
            }
            s_config_staged = false;
        }
        portEXIT_CRITICAL(&s_keypad_spinlock);

        if (move_pins) {
            // gpio_config and ISR (de)registration cannot run inside the spinlock
            esp_err_t err = board_keys_set_gpio(applied.key1_gpio, applied.key2_gpio);
            if (err != ESP_OK) {
                // Keep the whole previous config, and its pins armed, so what
                // keypad_get_config reports is what the keys are really on
                ESP_LOGE(TAG, "Failed to move keys to GPIO%u/GPIO%u (%s), staying on GPIO%u/GPIO%u",
                         applied.key1_gpio, applied.key2_gpio, esp_err_to_name(err),
                         previous.key1_gpio, previous.key2_gpio);
                diag_record(DIAG_EVENT_CONFIG_REJECTED, 3 /* ERROR */, (uint32_t)err,
                            ((uint32_t)applied.key1_gpio << 8) | applied.key2_gpio);
                esp_err_t rearm = board_keys_set_gpio(previous.key1_gpio, previous.key2_gpio);
                if (rearm != ESP_OK) {
                    ESP_LOGE(TAG, "Re-arming GPIO%u/GPIO%u failed: %s",
                             previous.key1_gpio, previous.key2_gpio, esp_err_to_name(rearm));
                }
                applied = previous;
            }
            portENTER_CRITICAL(&s_keypad_spinlock);
            s_config = applied;
            usb_hid_set_keycodes(applied.keycode1, applied.keycode2);
            portEXIT_CRITICAL(&s_keypad_spinlock);
            // Start debouncing from the new pins; a switch already held down is reported
            if (restart_debounce_from_pins()) {
                xTaskNotifyGive(s_input_task_handle);
            }
        }

        // 4. Pin detection
        detect_scan_step(&scan);

        // 5. Key line test (board test, IDLE only)
        line_test_step();
    }
}

esp_err_t keypad_init(const keypad_config_t *config)
{
    if (config) {
        keypad_set_config(config);
    } else {
        s_config.keycode1 = 0x1D;
        s_config.keycode2 = 0x1B;
        s_config.debounce_us = DEBOUNCE_DEFAULT_US;
        s_config.key1_gpio = KEYPAD_DEFAULT_KEY1_GPIO;
        s_config.key2_gpio = KEYPAD_DEFAULT_KEY2_GPIO;
    }

    esp_err_t err = board_keys_set_gpio(s_config.key1_gpio, s_config.key2_gpio);
    if (err != ESP_OK) {
        ESP_LOGW(TAG, "Key GPIO%u/GPIO%u rejected (%s), using GPIO%d/GPIO%d",
                 s_config.key1_gpio, s_config.key2_gpio, esp_err_to_name(err),
                 KEYPAD_DEFAULT_KEY1_GPIO, KEYPAD_DEFAULT_KEY2_GPIO);
        s_config.key1_gpio = KEYPAD_DEFAULT_KEY1_GPIO;
        s_config.key2_gpio = KEYPAD_DEFAULT_KEY2_GPIO;
        err = board_keys_set_gpio(s_config.key1_gpio, s_config.key2_gpio);
        if (err != ESP_OK) {
            return err;
        }
    }

#if defined(CONFIG_OSUPAD_BENCH_DEBUG_GPIO) || defined(OSUPAD_BENCH_DEBUG_GPIO)
    gpio_config_t dbg_io_conf = {
        .pin_bit_mask = (1ULL << CONFIG_OSUPAD_BENCH_DEBUG_GPIO_NUM),
        .mode = GPIO_MODE_OUTPUT,
        .pull_up_en = GPIO_PULLUP_DISABLE,
        .pull_down_en = GPIO_PULLDOWN_ENABLE,
        .intr_type = GPIO_INTR_DISABLE,
    };
    gpio_config(&dbg_io_conf);
    gpio_set_level(CONFIG_OSUPAD_BENCH_DEBUG_GPIO_NUM, 0);
    ESP_LOGI(TAG, "Debug GPIO initialized on pin %d", CONFIG_OSUPAD_BENCH_DEBUG_GPIO_NUM);
#endif

    // Initial state read
    bool k1_init = read_key_level(0);
    bool k2_init = read_key_level(1);
    debounce_init(&s_key_debounce[0], k1_init);
    debounce_init(&s_key_debounce[1], k2_init);
    s_key_state[0] = k1_init;
    s_key_state[1] = k2_init;

    // Spawn high-priority task (configMAX_PRIORITIES - 1) pinned to Core 0
    BaseType_t res = xTaskCreatePinnedToCore(
        keypad_task,
        "keypad_task",
        4096,
        NULL,
        configMAX_PRIORITIES - 1,
        &s_input_task_handle,
        0
    );
    if (res != pdPASS) {
        ESP_LOGE(TAG, "Failed to create keypad task");
        return ESP_FAIL;
    }

    // Register board GPIO ISR
    err = board_keys_register_isr(gpio_isr_handler);
    if (err != ESP_OK) {
        ESP_LOGE(TAG, "Failed to register keypad ISR: %s", esp_err_to_name(err));
        return err;
    }

    ESP_LOGI(TAG, "Keypad initialized (debouncing=%lu us, Key1: 0x%02X@GPIO%u, Key2: 0x%02X@GPIO%u)",
             (unsigned long)s_config.debounce_us, s_config.keycode1, s_config.key1_gpio,
             s_config.keycode2, s_config.key2_gpio);
    return ESP_OK;
}

void keypad_set_state_callback(keypad_state_callback_t cb)
{
    s_callback = cb;
}

bool keypad_is_pressed(keypad_key_id_t key_id)
{
    if (key_id < KEY_ID_COUNT) {
        return s_key_state[key_id];
    }
    return false;
}

void keypad_get_lifetime_presses(uint64_t *key1_presses, uint64_t *key2_presses)
{
    if (key1_presses) {
        *key1_presses = atomic_load_explicit(&s_key1_lifetime_presses, memory_order_relaxed);
    }
    if (key2_presses) {
        *key2_presses = atomic_load_explicit(&s_key2_lifetime_presses, memory_order_relaxed);
    }
}

void keypad_set_lifetime_presses(uint64_t key1_presses, uint64_t key2_presses)
{
    atomic_store_explicit(&s_key1_lifetime_presses, key1_presses, memory_order_relaxed);
    atomic_store_explicit(&s_key2_lifetime_presses, key2_presses, memory_order_relaxed);
}

void keypad_add_lifetime_presses(uint64_t key1_presses, uint64_t key2_presses)
{
    atomic_fetch_add_explicit(&s_key1_lifetime_presses, key1_presses, memory_order_relaxed);
    atomic_fetch_add_explicit(&s_key2_lifetime_presses, key2_presses, memory_order_relaxed);
}

void keypad_get_map_presses(uint32_t *key1_presses, uint32_t *key2_presses)
{
    if (key1_presses) {
        *key1_presses = atomic_load_explicit(&s_key1_map_presses, memory_order_relaxed);
    }
    if (key2_presses) {
        *key2_presses = atomic_load_explicit(&s_key2_map_presses, memory_order_relaxed);
    }
}

void keypad_reset_map_presses(void)
{
    atomic_store_explicit(&s_key1_map_presses, 0, memory_order_relaxed);
    atomic_store_explicit(&s_key2_map_presses, 0, memory_order_relaxed);
}

int64_t keypad_get_last_press_us(keypad_key_id_t key_id)
{
    if (key_id == KEY_ID_1) return atomic_load_explicit(&s_key1_last_press_us, memory_order_relaxed);
    if (key_id == KEY_ID_2) return atomic_load_explicit(&s_key2_last_press_us, memory_order_relaxed);
    return 0;
}

void keypad_set_config(const keypad_config_t *config)
{
    if (!config) {
        return;
    }

    keypad_config_t clamped = *config;
    if (clamped.debounce_us < DEBOUNCE_MIN_US) {
        clamped.debounce_us = DEBOUNCE_MIN_US;
    } else if (clamped.debounce_us > DEBOUNCE_MAX_US) {
        clamped.debounce_us = DEBOUNCE_MAX_US;
    }

    if (s_input_task_handle == NULL) {
        // Before keypad_init: pins are configured from s_config there
        s_config = clamped;
        usb_hid_set_keycodes(clamped.keycode1, clamped.keycode2);
        return;
    }

    // Applied by the keypad task once both keys are released and reported so:
    // new keycodes never land in a report while a key is held, and pin moves
    // stay with the only task touching key GPIOs
    portENTER_CRITICAL(&s_keypad_spinlock);
    s_staged_config = clamped;
    s_config_staged = true;
    portEXIT_CRITICAL(&s_keypad_spinlock);
    xTaskNotifyGive(s_input_task_handle);
}

void keypad_get_config(keypad_config_t *out_config)
{
    if (out_config) {
        portENTER_CRITICAL(&s_keypad_spinlock);
        *out_config = s_config;
        portEXIT_CRITICAL(&s_keypad_spinlock);
    }
}

uint32_t keypad_detect_pin_start(uint32_t timeout_ms, uint32_t exclude_gpio)
{
    if (s_input_task_handle == NULL || !s_input_enabled) {
        return 0; // also with an HE module: its analog outputs would read as a pin
    }
    portENTER_CRITICAL(&s_keypad_spinlock);
    uint32_t id = ++s_detect_req_id;
    if (id == 0) {
        id = ++s_detect_req_id; // 0 means "not started"
    }
    s_detect_req_timeout_ms = timeout_ms;
    s_detect_req_exclude = exclude_gpio;
    portEXIT_CRITICAL(&s_keypad_spinlock);
    xTaskNotifyGive(s_input_task_handle);
    return id;
}

bool keypad_detect_pin_result(uint32_t id, int *out_pin)
{
    portENTER_CRITICAL(&s_keypad_spinlock);
    bool done = id != 0 && s_detect_done_id == id;
    int pin = s_detect_done_pin;
    portEXIT_CRITICAL(&s_keypad_spinlock);
    if (done && out_pin) {
        *out_pin = pin;
    }
    return done;
}

void keypad_set_input_enabled(bool enabled)
{
    s_input_enabled = enabled;
    if (s_input_task_handle == NULL) {
        return; // keypad_init reads the pins with this in effect
    }
    // Start again from the pins as they read now (released when off)
    restart_debounce_from_pins();
    xTaskNotifyGive(s_input_task_handle);
}

// Long enough for the keypad task to get round to it between key events
#define LINE_TEST_WAIT_MS 100

esp_err_t keypad_line_test(keypad_line_test_t *out)
{
    if (!out) {
        return ESP_ERR_INVALID_ARG;
    }
    if (s_input_task_handle == NULL) {
        return ESP_ERR_INVALID_STATE;
    }
    portENTER_CRITICAL(&s_keypad_spinlock);
    uint32_t id = ++s_line_test_req_id;
    portEXIT_CRITICAL(&s_keypad_spinlock);
    xTaskNotifyGive(s_input_task_handle);

    for (int waited = 0; waited < LINE_TEST_WAIT_MS; waited++) {
        vTaskDelay(pdMS_TO_TICKS(1) ? pdMS_TO_TICKS(1) : 1);
        portENTER_CRITICAL(&s_keypad_spinlock);
        bool done = s_line_test_done_id == id;
        if (done) {
            *out = s_line_test_result;
        }
        portEXIT_CRITICAL(&s_keypad_spinlock);
        if (done) {
            return ESP_OK;
        }
    }
    return ESP_ERR_TIMEOUT;
}
