OPad-dev/OPad/desktop/daemon/src/ipc_handlers.rs

use parking_lot::Mutex;
use std::sync::Arc;
use std::time::Duration;
use tracing::{info, warn};

use opad_device::DeviceEvent;
use opad_ipc::{
    read_request, send_response, CurrentBackupState, IpcRequest, IpcResponse, IpcTransport,
    UpdateComponent, IPC_PROTOCOL_VERSION,
};
use opad_layout::Screen;
use opad_model::{char_to_hid_usage, CounterState, DeviceConfig, DeviceInfo, RuntimeMode};
use opad_storage::Storage;

use crate::identity;
use crate::log_hub::LogHub;
use crate::runtime::{DaemonState, PendingCounterReset, PendingOperations};
use crate::sync::{perform_sync, DeviceLink};
use crate::updater::{self, UpdateService};

/// The pad takes about 30 ms; this covers a busy USB link and a slow protocol task
const BOARD_TEST_TIMEOUT: Duration = Duration::from_secs(3);

/// Resolves a pending takeover without asking when the pad has at least as many
/// presses as this PC on both keys: the pad is taken over keeping its own
/// counters, exactly as if the user had picked that, so nothing is lost. When
/// this PC is ahead the prompt stays for the user. Returns whether it resolved.
pub async fn take_over_if_pad_is_ahead<D: DeviceLink>(
    state: &Arc<Mutex<DaemonState>>,
    storage: &Arc<Mutex<Option<Storage>>>,
    device: &D,
    log_hub: &LogHub,
    pending_ops: &Arc<Mutex<PendingOperations>>,
) -> bool {
    let (pending, st_pc) = {
        let st = state.lock();
        (st.pending_takeover.clone(), st.pc_counters.clone())
    };
    let Some(pending) = pending else {
        return false;
    };
    // This PC's counters for this pad; none means it has never counted for it
    let pc = storage
        .lock()
        .as_ref()
        .and_then(|s| s.load_device_state(&pending.device_id).unwrap_or(None))
        .or(st_pc.filter(|c| c.device_id == pending.device_id));
    let pad = CounterState {
        device_id: pending.device_id.clone(),
        lifetime_key1: pending.device_key1,
        lifetime_key2: pending.device_key2,
        ..Default::default()
    };
    if crate::runtime::pc_is_ahead(pc.as_ref(), &pad) {
        return false;
    }
    info!(
        "Pad {} is paired with another installation but has at least this PC's presses; taking it over without asking",
        pending.device_id
    );
    let resp = Box::pin(handle_ipc_request(
        IpcRequest::ResolveTakeover {
            take_over: true,
            keep_device_counters: true,
        },
        state,
        storage,
        device,
        log_hub,
        pending_ops,
        None,
    ))
    .await;
    matches!(resp, IpcResponse::CountersRestored { .. })
}

/// The refusal every pad-writing handler returns while
/// [`DaemonState::pad_guard`] says the connected pad must be left alone.
fn refuse_if_pad_guarded(state: &Arc<Mutex<DaemonState>>) -> Option<IpcResponse> {
    state
        .lock()
        .pad_guard()
        .map(|reason| IpcResponse::Error(reason.to_string()))
}

pub async fn handle_ipc_request<D: DeviceLink>(
    req: IpcRequest,
    state: &Arc<Mutex<DaemonState>>,
    storage: &Arc<Mutex<Option<Storage>>>,
    device: &D,
    log_hub: &LogHub,
    pending_ops: &Arc<Mutex<PendingOperations>>,
    updates: Option<&UpdateService>,
) -> IpcResponse {
    let mode = { state.lock().mode };

    match req {
        IpcRequest::Handshake {
            client_protocol,
            client_version,
        } => {
            if client_protocol != IPC_PROTOCOL_VERSION {
                return IpcResponse::HandshakeRejected {
                    daemon_protocol: IPC_PROTOCOL_VERSION,
                    reason: format!(
                        "IPC protocol version mismatch: client is {}, daemon is {}",
                        client_protocol, IPC_PROTOCOL_VERSION
                    ),
                };
            }
            // §U-2: after an in-place app update the files on disk are new
            // while this process is still the old binary. A new GUI talking to
            // an old daemon must fail loudly, not misbehave subtly — the two
            // always ship together, so differing versions mean exactly this.
            let daemon_version = env!("CARGO_PKG_VERSION");
            if client_version != daemon_version {
                return IpcResponse::HandshakeRejected {
                    daemon_protocol: IPC_PROTOCOL_VERSION,
                    reason: format!(
                        "Version mismatch: this client is {} but the running daemon is {}. \
                         The app was updated; restart opad-daemon to finish.",
                        client_version, daemon_version
                    ),
                };
            }
            let st = state.lock();
            IpcResponse::HandshakeAck {
                daemon_version: env!("CARGO_PKG_VERSION").to_string(),
                daemon_protocol: IPC_PROTOCOL_VERSION,
                device_connected: st.device_connected,
            }
        }

        IpcRequest::GetStatus => {
            let st = state.lock();
            let pc_counters = if let Some(info) = &st.device_info {
                let s_guard = storage.lock();
                s_guard
                    .as_ref()
                    .and_then(|s| s.load_device_state(&info.device_id).unwrap_or(None))
                    .or_else(|| st.pc_counters.clone())
            } else {
                st.pc_counters.clone()
            };
            let takeover_prompt = st.pending_takeover.as_ref().map(|t| {
                let pc = pc_counters.clone().unwrap_or_default();
                Box::new(opad_ipc::TakeoverPrompt {
                    device_id: t.device_id.clone(),
                    device_key1: t.device_key1,
                    device_key2: t.device_key2,
                    pc_key1: pc.lifetime_key1,
                    pc_key2: pc.lifetime_key2,
                })
            });
            IpcResponse::Status {
                mode: st.mode,
                device_connected: st.device_connected,
                device_info: st.device_info.clone(),
                counters: st.counters.clone(),
                counters_source: st.counters_source,
                pc_counters,
                esp_counters: st.esp_counters.clone(),
                config: st.config.clone(),
                last_sync_time: st.last_sync_time.clone(),
                last_sync_error: st.last_sync_error.clone(),
                storage_error: st.storage_error.clone(),
                tosu_connected: st.tosu_connected,
                latency: st.latency,
                pending_replacement: st.pending_replacement.clone(),
                pending_takeover: takeover_prompt,
                incompatible: st.incompatible.clone(),
                last_backup: st.last_backup.clone(),
                foreign_pad: st.foreign_pad,
            }
        }

        IpcRequest::GetLayouts => {
            let st = state.lock();
            IpcResponse::Layouts {
                idle: st.custom_layouts.get(&Screen::Idle).cloned(),
                playing: st.custom_layouts.get(&Screen::Playing).cloned(),
            }
        }

        IpcRequest::SetLayout { screen, layout } => {
            if let Some(refused) = refuse_if_pad_guarded(state) {
                return refused;
            }
            if let Err(e) = layout.validate() {
                return IpcResponse::OperationRejected {
                    reason: format!("Invalid layout: {}", e),
                };
            }
            state.lock().custom_layouts.insert(screen, layout.clone());
            if mode == RuntimeMode::Playing || mode == RuntimeMode::Cooldown {
                let _ = device.send_layout(screen, &layout).await;
                pending_ops
                    .lock()
                    .pending_layouts
                    .push((screen, Some(layout)));
                return IpcResponse::LayoutApplied {
                    screen,
                    message: "Layout applied to pad RAM; will be saved after gameplay".to_string(),
                };
            }
            if let Some(s) = storage.lock().as_ref() {
                if let Err(e) = s.save_layout(screen.to_wire(), &layout.to_json()) {
                    warn!("Failed to save layout: {}", e);
                }
            }
            info!("Layout {} saved", screen.label());
            if !state.lock().device_connected {
                return IpcResponse::LayoutApplied {
                    screen,
                    message: "Saved; it will be applied when the pad connects".to_string(),
                };
            }
            let mut events = device.subscribe();
            if let Err(e) = device.send_layout(screen, &layout).await {
                return IpcResponse::Error(format!("Failed to send layout: {}", e));
            }
            wait_for_layout_ack(&mut events, screen).await
        }

        IpcRequest::ResetLayout { screen } => {
            if let Some(refused) = refuse_if_pad_guarded(state) {
                return refused;
            }
            state.lock().custom_layouts.remove(&screen);
            if mode == RuntimeMode::Playing || mode == RuntimeMode::Cooldown {
                let _ = device.reset_layout(screen).await;
                pending_ops.lock().pending_layouts.push((screen, None));
                return IpcResponse::LayoutApplied {
                    screen,
                    message: "Layout reset in pad RAM; will be saved after gameplay".to_string(),
                };
            }
            if let Some(s) = storage.lock().as_ref() {
                if let Err(e) = s.delete_layout(screen.to_wire()) {
                    warn!("Failed to delete layout: {}", e);
                }
            }
            info!("Layout {} reset to default", screen.label());
            if !state.lock().device_connected {
                return IpcResponse::LayoutApplied {
                    screen,
                    message: "Reset; the pad will use its default".to_string(),
                };
            }
            let mut events = device.subscribe();
            if let Err(e) = device.reset_layout(screen).await {
                return IpcResponse::Error(format!("Failed to reset layout: {}", e));
            }
            wait_for_layout_ack(&mut events, screen).await
        }

        IpcRequest::GetUiValues => {
            // Everything the pad is shown: tosu's values plus the tap rate the
            // daemon works out, so the designer's live preview has PPM too
            let st = state.lock();
            let tap = &st.tap.snapshot;
            let mut values = st.ui_values.clone();
            values.extend(opad_model::tap_rate::attempt_ui_values(
                tap.current.as_ref().or(tap.last.as_ref()),
            ));
            values.extend(opad_model::tap_rate::history_ui_values(
                tap.history.as_ref(),
            ));
            IpcResponse::UiValues(values)
        }

        IpcRequest::GetTapStats => IpcResponse::TapStats(state.lock().tap.snapshot.clone()),

        IpcRequest::SetTapHistoryPeriod { days } => {
            if let Err(e) = opad_model::tap_rate::validate_history_days(days) {
                return IpcResponse::Error(e);
            }
            // The history is a read, allowed in any mode; the setting is a
            // write, so during gameplay it waits for IDLE (P1-3) and applies
            // in memory meanwhile
            let (history, saved) = match storage.lock().as_ref() {
                Some(s) => (
                    s.tap_history(days, chrono::Utc::now())
                        .map_err(|e| warn!("Cannot read the tap rate history: {}", e))
                        .ok(),
                    s.set_tap_history_days(days).is_ok(),
                ),
                None => (None, false),
            };
            let mut st = state.lock();
            st.tap.snapshot.period_days = days;
            st.tap.snapshot.history = history;
            st.tap.period_unsaved = !saved;
            IpcResponse::TapStats(st.tap.snapshot.clone())
        }

        IpcRequest::GetUpdateStatus => {
            let Some(updates) = updates else {
                return IpcResponse::Error("The update worker is not running".to_string());
            };
            let status = updates.status();
            IpcResponse::UpdateStatus {
                app: status.app,
                tosu: status.tosu,
                last_check: status.last_check.map(|t| {
                    chrono::DateTime::<chrono::Utc>::from(t)
                        .to_rfc3339_opts(chrono::SecondsFormat::Secs, true)
                }),
                last_error: status.last_error,
                restart_required: status.restart_required,
            }
        }

        IpcRequest::SetUpdateEnabled { component, enabled } => {
            let key = match component {
                UpdateComponent::App => updater::APP_ENABLED_KEY,
                UpdateComponent::Tosu => updater::TOSU_ENABLED_KEY,
                // §U-3: firmware updates take explicit consent each time, so
                // there is no "leave it on" setting to write.
                UpdateComponent::Firmware => {
                    return IpcResponse::OperationRejected {
                        reason: "Firmware updates are consented to individually, not enabled"
                            .to_string(),
                    }
                }
            };
            let guard = storage.lock();
            match guard.as_ref() {
                Some(s) => match s.set_app_state(key, if enabled { "1" } else { "0" }) {
                    Ok(()) => IpcResponse::ConfigUpdated {
                        config: state.lock().config.clone(),
                        deferred_persist: false,
                    },
                    // Mid-map this is a blocked storage write, not a failure
                    Err(e) => IpcResponse::OperationDeferred {
                        reason: format!("Cannot save the update setting right now: {}", e),
                    },
                },
                None => IpcResponse::Error("Storage is unavailable".to_string()),
            }
        }

        IpcRequest::InstallUpdate { component } => {
            // The play-state gate comes first, before any question about
            // plumbing: §U-0.1 holds whether or not an updater is running.
            if mode != RuntimeMode::Idle {
                return IpcResponse::OperationDeferred {
                    reason: format!("Cannot install an update while the daemon is {:?}", mode),
                };
            }
            let Some(updates) = updates else {
                return IpcResponse::Error("The update worker is not running".to_string());
            };
            match updates.request_install(component) {
                Ok(()) => IpcResponse::UpdateStarted { component },
                Err(e) => IpcResponse::Error(e),
            }
        }

        IpcRequest::ResetLatencyStats => {
            if let Err(e) = device.reset_latency_stats().await {
                return IpcResponse::Error(format!("Failed to reset latency stats: {}", e));
            }
            state.lock().latency = None;
            info!("Latency statistics reset");
            IpcResponse::HandshakeAck {
                daemon_version: env!("CARGO_PKG_VERSION").to_string(),
                daemon_protocol: IPC_PROTOCOL_VERSION,
                device_connected: state.lock().device_connected,
            }
        }

        IpcRequest::UpdateConfig(new_config) => {
            if let Some(refused) = refuse_if_pad_guarded(state) {
                return refused;
            }
            if let Err(e) = new_config.validate() {
                return IpcResponse::OperationRejected {
                    reason: format!("Invalid configuration: {}", e),
                };
            }

            let current_cfg = { state.lock().config.clone() };

            if mode == RuntimeMode::Playing || mode == RuntimeMode::Cooldown {
                let keys_or_debounce_changed = current_cfg.key1_hid_usage
                    != new_config.key1_hid_usage
                    || current_cfg.key2_hid_usage != new_config.key2_hid_usage
                    || current_cfg.debounce_us != new_config.debounce_us
                    || current_cfg.key1_gpio != new_config.key1_gpio
                    || current_cfg.key2_gpio != new_config.key2_gpio;

                if keys_or_debounce_changed {
                    pending_ops.lock().pending_config = Some(new_config);
                    return IpcResponse::OperationDeferred {
                        reason:
                            "Key mapping, pin and debounce changes are deferred until IDLE mode"
                                .to_string(),
                    };
                }

                // Brightness / sleep / hz changes are applied to RAM immediately (§P1-3)
                let _ = device.send_config(&new_config).await;
                {
                    let mut st = state.lock();
                    st.config = new_config.clone();
                }
                pending_ops.lock().pending_config = Some(new_config.clone());
                info!("Configuration applied to RAM (persistence queued for SYNC)");
                return IpcResponse::ConfigUpdated {
                    config: new_config,
                    deferred_persist: true,
                };
            }

            if let Some(s) = storage.lock().as_ref() {
                if let Err(e) = s.save_config(&new_config) {
                    return IpcResponse::Error(format!("Failed to save config: {}", e));
                }
            }

            {
                let mut st = state.lock();
                st.config = new_config.clone();
            }

            let _ = device.send_config(&new_config).await;
            info!("Configuration updated");
            IpcResponse::ConfigUpdated {
                config: new_config,
                deferred_persist: false,
            }
        }

        IpcRequest::ForceSync => {
            if let Some(refused) = refuse_if_pad_guarded(state) {
                return refused;
            }
            if mode == RuntimeMode::Playing || mode == RuntimeMode::Cooldown {
                return IpcResponse::OperationRejected {
                    reason: "Cannot force synchronization during gameplay or cooldown".to_string(),
                };
            }
            if storage.lock().is_none() {
                return IpcResponse::OperationRejected {
                    reason:
                        "Database unavailable: counter sync is rejected without persistent storage"
                            .to_string(),
                };
            }
            match perform_sync(state, storage, device, pending_ops).await {
                Ok(counters) => IpcResponse::SyncCompleted {
                    success: true,
                    counters,
                },
                Err(e) => IpcResponse::Error(format!("Sync failed: {}", e)),
            }
        }

        IpcRequest::ResetCounters { confirm } => {
            if let Some(refused) = refuse_if_pad_guarded(state) {
                return refused;
            }
            if !confirm {
                return IpcResponse::OperationRejected {
                    reason: "ResetCounters requires explicit confirmation (--yes or modal confirm)"
                        .to_string(),
                };
            }

            if mode == RuntimeMode::Playing || mode == RuntimeMode::Cooldown {
                return IpcResponse::OperationRejected {
                    reason: "Cannot reset counters during gameplay or cooldown".to_string(),
                };
            }

            if storage.lock().is_none() {
                return IpcResponse::OperationRejected {
                    reason:
                        "Database unavailable: counter reset is rejected without persistent storage"
                            .to_string(),
                };
            }

            let (updated, target) = {
                let mut st = state.lock();
                st.counters.counter_generation = st.counters.counter_generation.saturating_add(1);
                st.counters.lifetime_key1 = 0;
                st.counters.lifetime_key2 = 0;
                let updated = st.counters.clone();

                if let Some(info) = &st.device_info {
                    if let Some(s) = storage.lock().as_ref() {
                        let _ = s.save_device_state(info, &updated);
                    }
                }
                (
                    updated,
                    st.device_info.as_ref().map(|i| i.device_id.clone()),
                )
            };

            if state.lock().device_connected {
                let _ = device.send_counter_sync(&updated, true).await;
            } else {
                // Honoured by the next sync with this pad (perform_sync)
                pending_ops.lock().pending_device_push =
                    Some(PendingCounterReset { device_id: target });
            }
            info!("Lifetime counters reset with incremented generation");
            IpcResponse::CountersReset { counters: updated }
        }

        IpcRequest::RestoreDeviceFromPc { confirm } => {
            if let Some(refused) = refuse_if_pad_guarded(state) {
                return refused;
            }
            if mode == RuntimeMode::Playing || mode == RuntimeMode::Cooldown {
                return IpcResponse::OperationRejected {
                    reason: "Cannot restore counters during active gameplay or cooldown"
                        .to_string(),
                };
            }
            if !confirm {
                return IpcResponse::OperationRejected {
                    reason: "Confirmation required to force-restore ESP counters from PC"
                        .to_string(),
                };
            }
            if storage.lock().is_none() {
                return IpcResponse::OperationRejected {
                    reason: "Database unavailable: restore from PC is rejected without persistent storage"
                        .to_string(),
                };
            }
            let (info_opt, in_memory_counters, is_connected) = {
                let st = state.lock();
                (
                    st.device_info.clone(),
                    st.counters.clone(),
                    st.device_connected,
                )
            };
            let Some(info) = info_opt else {
                return IpcResponse::OperationRejected {
                    reason: "No device currently connected".to_string(),
                };
            };
            if !is_connected {
                return IpcResponse::OperationRejected {
                    reason: "Device is disconnected".to_string(),
                };
            }

            let pc_state = {
                let s_guard = storage.lock();
                s_guard
                    .as_ref()
                    .and_then(|s| s.load_device_state(&info.device_id).unwrap_or(None))
            };
            let Some(pc_counters) = pc_state else {
                return IpcResponse::OperationRejected {
                    reason: "No PC counter state found in database for this device".to_string(),
                };
            };

            let new_gen = std::cmp::max(
                pc_counters.counter_generation,
                in_memory_counters.counter_generation,
            )
            .saturating_add(1);
            let target = CounterState {
                device_id: info.device_id.clone(),
                counter_generation: new_gen,
                lifetime_key1: pc_counters.lifetime_key1,
                lifetime_key2: pc_counters.lifetime_key2,
                map_key1: 0,
                map_key2: 0,
            };

            if let Some(s) = storage.lock().as_ref() {
                let _ = s.save_device_state(&info, &target);
                let _ = s.touch_device_last_seen(&info.device_id);
            }

            let _ = device.send_counter_sync(&target, true).await;
            {
                let mut st = state.lock();
                st.counters = target.clone();
                st.pc_counters = Some(target.clone());
                st.esp_counters = Some(target.clone());
            }
            info!(
                "Force-restored ESP counters from PC (generation: {})",
                new_gen
            );
            IpcResponse::CountersRestored { counters: target }
        }

        IpcRequest::ImportPcFromDevice { confirm } => {
            if let Some(refused) = refuse_if_pad_guarded(state) {
                return refused;
            }
            if mode == RuntimeMode::Playing || mode == RuntimeMode::Cooldown {
                return IpcResponse::OperationRejected {
                    reason: "Cannot import counters during active gameplay or cooldown".to_string(),
                };
            }
            if !confirm {
                return IpcResponse::OperationRejected {
                    reason: "Confirmation required to overwrite PC counters from ESP".to_string(),
                };
            }
            if storage.lock().is_none() {
                return IpcResponse::OperationRejected {
                    reason: "Database unavailable: import from device is rejected without persistent storage"
                        .to_string(),
                };
            }
            let (info_opt, in_memory_counters, is_connected) = {
                let st = state.lock();
                (
                    st.device_info.clone(),
                    st.counters.clone(),
                    st.device_connected,
                )
            };
            let Some(info) = info_opt else {
                return IpcResponse::OperationRejected {
                    reason: "No device currently connected".to_string(),
                };
            };
            if !is_connected {
                return IpcResponse::OperationRejected {
                    reason: "Device is disconnected".to_string(),
                };
            }

            let pc_state = {
                let s_guard = storage.lock();
                s_guard
                    .as_ref()
                    .and_then(|s| s.load_device_state(&info.device_id).unwrap_or(None))
            };
            let pc_gen = pc_state.as_ref().map(|c| c.counter_generation).unwrap_or(0);

            let new_gen =
                std::cmp::max(pc_gen, in_memory_counters.counter_generation).saturating_add(1);
            let target = CounterState {
                device_id: info.device_id.clone(),
                counter_generation: new_gen,
                lifetime_key1: in_memory_counters.lifetime_key1,
                lifetime_key2: in_memory_counters.lifetime_key2,
                map_key1: 0,
                map_key2: 0,
            };

            if let Some(s) = storage.lock().as_ref() {
                let _ = s.save_device_state(&info, &target);
                let _ = s.touch_device_last_seen(&info.device_id);
            }

            let _ = device.send_counter_sync(&target, true).await;
            {
                let mut st = state.lock();
                st.counters = target.clone();
                st.pc_counters = Some(target.clone());
                st.esp_counters = Some(target.clone());
            }
            info!(
                "Overwrote PC database counters from ESP (generation: {})",
                new_gen
            );
            IpcResponse::CountersRestored { counters: target }
        }

        IpcRequest::ResolveTakeover {
            take_over,
            keep_device_counters,
        } => {
            // P1-3: taking over writes NVS on the pad and SQLite here.
            if mode == RuntimeMode::Playing || mode == RuntimeMode::Cooldown {
                return IpcResponse::OperationDeferred {
                    reason: "Cannot resolve pad ownership during gameplay or cooldown".to_string(),
                };
            }

            let (pending, info_opt, device_counters, install_id) = {
                let mut st = state.lock();
                (
                    st.pending_takeover.take(),
                    st.device_info.clone(),
                    st.counters.clone(),
                    st.install_id.clone(),
                )
            };
            let Some(pending) = pending else {
                return IpcResponse::OperationRejected {
                    reason: "No pad is waiting on an ownership decision".to_string(),
                };
            };
            let Some(info) = info_opt else {
                return IpcResponse::OperationRejected {
                    reason: "No device currently connected".to_string(),
                };
            };

            if !take_over {
                // "Leave it alone": nothing is written to the pad and nothing
                // is synced from it. It stays a working keyboard (§A.6.1).
                info!(
                    "Leaving pad {} with its current owner; telemetry and config stay off",
                    pending.device_id
                );
                return IpcResponse::OperationRejected {
                    reason: "Left the pad paired with its other installation".to_string(),
                };
            }

            if storage.lock().is_none() {
                // Put the prompt back: an unanswerable takeover must not be
                // silently forgotten.
                state.lock().pending_takeover = Some(pending);
                return IpcResponse::OperationRejected {
                    reason: "Database unavailable: taking over a pad needs persistent storage"
                        .to_string(),
                };
            }

            // The pad is ours from here. Which counters survive is the user's
            // choice, and is applied before anything is saved, so no counter is
            // ever written under the wrong owner (§W3-3).
            let pc_state = {
                let s_guard = storage.lock();
                s_guard
                    .as_ref()
                    .and_then(|s| s.load_device_state(&info.device_id).unwrap_or(None))
            };
            let pc_gen = pc_state.as_ref().map(|c| c.counter_generation).unwrap_or(0);
            let new_gen =
                std::cmp::max(pc_gen, device_counters.counter_generation).saturating_add(1);

            let (key1, key2) = if keep_device_counters {
                (device_counters.lifetime_key1, device_counters.lifetime_key2)
            } else {
                pc_state
                    .as_ref()
                    .map(|c| (c.lifetime_key1, c.lifetime_key2))
                    .unwrap_or((0, 0))
            };
            let target = CounterState {
                device_id: info.device_id.clone(),
                counter_generation: new_gen,
                lifetime_key1: key1,
                lifetime_key2: key2,
                map_key1: 0,
                map_key2: 0,
            };

            // Record the new owner on the pad itself *before* anything else,
            // and refuse the takeover if it does not stick. Without this the
            // pad still names the other install and would prompt again on the
            // next connect, which §W3-3 says must not happen.
            let Some(owner) = install_id.as_deref().and_then(identity::parse_owner_id) else {
                state.lock().pending_takeover = Some(pending);
                return IpcResponse::OperationRejected {
                    reason: "This install has no identity, so it cannot take a pad over"
                        .to_string(),
                };
            };
            if let Err(e) = device.claim_ownership(&owner).await {
                state.lock().pending_takeover = Some(pending);
                return IpcResponse::Error(format!("Could not record ownership on the pad: {}", e));
            }

            if let Some(s) = storage.lock().as_ref() {
                let _ = s.save_device_state(&info, &target);
                let _ = s.touch_device_last_seen(&info.device_id);
            }
            let _ = device.send_counter_sync(&target, true).await;
            // The pad is ours now, so the config we suppressed while it was
            // foreign goes out (§W3-3)...
            // ...and so do the custom layouts, held back on connect under the
            // same condition
            let (config, layouts) = {
                let st = state.lock();
                (st.config.clone(), st.custom_layouts.clone())
            };
            let _ = device.send_config(&config).await;
            for (screen, layout) in &layouts {
                let _ = device.send_layout(*screen, layout).await;
            }
            {
                let mut st = state.lock();
                st.foreign_pad = false;
                st.counters = target.clone();
                st.pc_counters = Some(target.clone());
                st.esp_counters = Some(target.clone());
            }
            info!(
                "Took over pad {} (keeping {} counters, generation {})",
                info.device_id,
                if keep_device_counters {
                    "the pad's"
                } else {
                    "this PC's"
                },
                new_gen
            );
            IpcResponse::CountersRestored { counters: target }
        }

        IpcRequest::ResolveReplacement { restore } => {
            if mode == RuntimeMode::Playing || mode == RuntimeMode::Cooldown {
                return IpcResponse::OperationRejected {
                    reason: "Cannot resolve replacement during gameplay or cooldown".to_string(),
                };
            }
            if storage.lock().is_none() {
                return IpcResponse::OperationRejected {
                    reason: "Database unavailable: resolving replacement is rejected without persistent storage"
                        .to_string(),
                };
            }

            let (old_device_id_opt, current_info_opt, current_counters) = {
                let mut st = state.lock();
                (
                    st.pending_replacement.take(),
                    st.device_info.clone(),
                    st.counters.clone(),
                )
            };

            let Some(current_info) = current_info_opt else {
                return IpcResponse::OperationRejected {
                    reason: "No device currently connected to resolve replacement for".to_string(),
                };
            };

            if restore {
                if let Some(old_id) = old_device_id_opt {
                    let old_state = {
                        let s_guard = storage.lock();
                        s_guard
                            .as_ref()
                            .and_then(|s| s.load_device_state(&old_id).unwrap_or(None))
                    };
                    if let Some(old_c) = old_state {
                        let new_gen = std::cmp::max(
                            old_c.counter_generation,
                            current_counters.counter_generation,
                        )
                        .saturating_add(1);
                        let restored = CounterState {
                            device_id: current_info.device_id.clone(),
                            counter_generation: new_gen,
                            lifetime_key1: old_c.lifetime_key1,
                            lifetime_key2: old_c.lifetime_key2,
                            map_key1: 0,
                            map_key2: 0,
                        };
                        if let Some(s) = storage.lock().as_ref() {
                            let _ = s.save_device_state(&current_info, &restored);
                            let _ = s.touch_device_last_seen(&current_info.device_id);
                        }
                        let _ = device.send_counter_sync(&restored, true).await;
                        state.lock().counters = restored.clone();
                        info!("Restored lifetime counters from previous pad");
                        return IpcResponse::CountersReset { counters: restored };
                    }
                }
                IpcResponse::OperationRejected {
                    reason: "No previous device state found to restore from".to_string(),
                }
            } else {
                // Treat as new pad: register it in SQLite
                if let Some(s) = storage.lock().as_ref() {
                    let _ = s.save_device_state(&current_info, &current_counters);
                    let _ = s.touch_device_last_seen(&current_info.device_id);
                }
                info!("Adopted new pad as separate device");
                IpcResponse::CountersReset {
                    counters: current_counters,
                }
            }
        }

        IpcRequest::ExportBackup => match crate::backup::current(state, storage) {
            // The same document the automatic backup writes (§21), built in
            // one place so a manual export and an automatic one cannot differ.
            Some(backup) => IpcResponse::BackupExported(backup),
            None => IpcResponse::OperationRejected {
                reason: "No counters known yet: connect the pad once".to_string(),
            },
        },

        IpcRequest::PreviewImport(backup) => {
            if let Err(err) = backup.validate() {
                return IpcResponse::Error(format!("Invalid backup: {}", err));
            }

            let st = state.lock();
            let current = Some(CurrentBackupState {
                device_id: st.counters.device_id.clone(),
                counter_generation: st.counters.counter_generation,
                lifetime_key1: st.counters.lifetime_key1,
                lifetime_key2: st.counters.lifetime_key2,
                config: st.config.clone(),
            });

            let device_id_matches = st.counters.device_id.is_empty()
                || st.counters.device_id == backup.device.device_id;
            let is_counter_rollback = backup.stats.lifetime_key1 < st.counters.lifetime_key1
                || backup.stats.lifetime_key2 < st.counters.lifetime_key2;

            let mut warnings = Vec::new();
            if !device_id_matches {
                warnings.push(format!(
                    "Device ID mismatch: backup is for '{}', current pad is '{}'",
                    backup.device.device_id, st.counters.device_id
                ));
            }
            if is_counter_rollback {
                warnings.push(
                    "Incoming lifetime counters are lower than current counters (counter rollback)"
                        .to_string(),
                );
            }
            if backup.device.counter_generation <= st.counters.counter_generation {
                warnings.push(
                    "Incoming counter generation is not greater than current generation; generation will be bumped"
                        .to_string(),
                );
            }

            IpcResponse::ImportPreview {
                current,
                incoming: backup,
                device_id_matches,
                is_counter_rollback,
                warnings,
            }
        }

        IpcRequest::ImportBackup { backup, confirm } => {
            if let Some(refused) = refuse_if_pad_guarded(state) {
                return refused;
            }
            if !confirm {
                return IpcResponse::OperationRejected {
                    reason:
                        "ImportBackup requires explicit confirmation (--yes or user confirmation)"
                            .to_string(),
                };
            }

            if mode == RuntimeMode::Playing || mode == RuntimeMode::Cooldown {
                return IpcResponse::OperationRejected {
                    reason: "Cannot import backup during gameplay or cooldown".to_string(),
                };
            }

            if storage.lock().is_none() {
                return IpcResponse::OperationRejected {
                    reason:
                        "Database unavailable: backup import is rejected without persistent storage"
                            .to_string(),
                };
            }

            if let Err(err) = backup.validate() {
                return IpcResponse::Error(format!("Invalid backup: {}", err));
            }

            let (current_tosu, current_gen) = {
                let st = state.lock();
                (
                    st.config.tosu_endpoint.clone(),
                    st.counters.counter_generation,
                )
            };

            let k1_usage = char_to_hid_usage(&backup.config.key1).unwrap_or(0x1D);
            let k2_usage = char_to_hid_usage(&backup.config.key2).unwrap_or(0x1B);

            let new_config = DeviceConfig {
                key1_hid_usage: k1_usage,
                key2_hid_usage: k2_usage,
                debounce_us: backup.config.debounce_us,
                brightness: backup.config.brightness,
                display_sleep_seconds: backup.config.display_sleep_seconds,
                gameplay_display_hz: backup.config.gameplay_display_hz,
                tosu_endpoint: current_tosu,
                key1_gpio: backup.config.key1_gpio,
                key2_gpio: backup.config.key2_gpio,
                swipe_left_action: backup.config.swipe_left_action,
                swipe_right_action: backup.config.swipe_right_action,
                swipe_left_key: backup.config.swipe_left_key,
                swipe_right_key: backup.config.swipe_right_key,
                swipe_up_action: backup.config.swipe_up_action,
                swipe_down_action: backup.config.swipe_down_action,
                swipe_up_key: backup.config.swipe_up_key,
                swipe_down_key: backup.config.swipe_down_key,
                swipe_up_modifiers: backup.config.swipe_up_modifiers,
                swipe_down_modifiers: backup.config.swipe_down_modifiers,
                swipe_left_modifiers: backup.config.swipe_left_modifiers,
                swipe_right_modifiers: backup.config.swipe_right_modifiers,
            };

            let new_counters = CounterState {
                device_id: backup.device.device_id.clone(),
                counter_generation: std::cmp::max(current_gen, backup.device.counter_generation)
                    .saturating_add(1),
                lifetime_key1: backup.stats.lifetime_key1,
                lifetime_key2: backup.stats.lifetime_key2,
                map_key1: 0,
                map_key2: 0,
            };

            if let Some(s) = storage.lock().as_ref() {
                let _ = s.save_config(&new_config);
                let last_firmware_version = state
                    .lock()
                    .device_info
                    .as_ref()
                    .map(|i| i.firmware_version.clone())
                    .or_else(|| {
                        s.list_device_states()
                            .ok()?
                            .into_iter()
                            .find(|(i, _)| i.device_id == backup.device.device_id)
                            .map(|(i, _)| i.firmware_version)
                    })
                    .unwrap_or_default();
                let info = DeviceInfo {
                    device_id: backup.device.device_id,
                    board_profile: backup.device.board_profile,
                    firmware_version: last_firmware_version,
                    protocol_version: 1,
                    running_partition: None,
                };
                let _ = s.save_device_state(&info, &new_counters);
            }

            {
                let mut st = state.lock();
                st.config = new_config.clone();
                st.counters = new_counters.clone();
            }

            let _ = device.send_config(&new_config).await;
            let _ = device.send_counter_sync(&new_counters, true).await;
            info!("JSON Backup imported and applied");

            IpcResponse::BackupImported {
                success: true,
                counters: new_counters,
                config: new_config,
            }
        }

        IpcRequest::GetLogEntries {
            since_seq,
            limit,
            level,
            source,
        } => {
            let (entries, latest_seq) =
                log_hub.get_matching_entries(since_seq, limit, level, source);
            IpcResponse::LogEntries {
                entries,
                latest_seq,
            }
        }

        IpcRequest::GetFirmwareUpdate => {
            let storage_available = storage.lock().is_some();
            IpcResponse::FirmwareUpdateOffer(crate::firmware_update::offer(
                updates.and_then(|u| u.manifest()).as_ref(),
                state,
                storage_available,
            ))
        }

        IpcRequest::InstallFirmwareUpdate { confirm } => {
            let manifest = updates.and_then(|u| u.manifest());
            match crate::firmware_update::install(
                manifest.as_ref(),
                confirm,
                state,
                storage,
                device,
                pending_ops,
            )
            .await
            {
                Ok(crate::firmware_update::FirmwareUpdateOutcome::Installed { from, to, info }) => {
                    IpcResponse::FirmwareUpdateFinished {
                        from,
                        to,
                        firmware_version: info.firmware_version.clone(),
                        running_partition: info.running_partition.clone(),
                        protocol_version: info.protocol_version,
                        compatible: info.protocol_version == opad_protocol::DEVICE_PROTOCOL_VERSION,
                    }
                }
                Ok(crate::firmware_update::FirmwareUpdateOutcome::Refused { reasons }) => {
                    IpcResponse::OperationRejected {
                        reason: reasons.join(" "),
                    }
                }
                // Everything that reaches here has either written nothing or
                // says plainly that it wrote something and the pad did not come
                // back. Neither is ever reported as a success.
                Err(e) => IpcResponse::Error(e.to_string()),
            }
        }

        IpcRequest::PrepareFlash => {
            if mode == RuntimeMode::Playing || mode == RuntimeMode::Cooldown {
                return IpcResponse::OperationRejected {
                    reason: "Cannot flash firmware during gameplay or cooldown".to_string(),
                };
            }
            info!("Releasing serial port for firmware flash...");
            if !device.pause_and_release(Duration::from_secs(2)).await {
                device.resume();
                return IpcResponse::OperationRejected {
                    reason: "Timed out waiting for the serial port to be released".to_string(),
                };
            }
            {
                let mut st = state.lock();
                st.device_connected = false;
            }
            let port = device.port().or_else(opad_device::find_target_port);
            IpcResponse::ReadyForFlash { port }
        }

        IpcRequest::FinishFlash => {
            info!("Flash finished, resuming device discovery and waiting for reconnect...");
            let mut events = device.subscribe();
            device.resume();

            let wait_res = tokio::time::timeout(Duration::from_secs(15), async {
                loop {
                    match events.recv().await {
                        Ok(DeviceEvent::Connected(info, _)) => return Ok(info),
                        Ok(_) | Err(tokio::sync::broadcast::error::RecvError::Lagged(_)) => {
                            continue
                        }
                        Err(_) => return Err("Event stream closed".to_string()),
                    }
                }
            })
            .await;

            match wait_res {
                Ok(Ok(info)) => {
                    let compatible =
                        info.protocol_version == opad_protocol::DEVICE_PROTOCOL_VERSION;
                    IpcResponse::FlashFinished {
                        firmware_version: info.firmware_version,
                        protocol_version: info.protocol_version,
                        compatible,
                    }
                }
                Ok(Err(e)) => IpcResponse::Error(format!("Flash verification failed: {}", e)),
                Err(_) => IpcResponse::Error(
                    "Device did not reconnect within 15 seconds after flash".to_string(),
                ),
            }
        }

        IpcRequest::ResumeDevice => {
            info!("Resuming device discovery (no post-flash verification requested)");
            device.resume();
            IpcResponse::DeviceResumed
        }

        IpcRequest::RunBoardTest => {
            if !device.is_connected() {
                return IpcResponse::Error("The pad is not connected".to_string());
            }
            if !device.supports_board_test() {
                return IpcResponse::Error(
                    "This pad's firmware has no board test. Update the firmware, then run it again."
                        .to_string(),
                );
            }
            let mut sub = device.subscribe();
            if let Err(e) = device.run_board_test().await {
                return IpcResponse::Error(format!("Could not ask the pad for a board test: {e}"));
            }
            let result = tokio::time::timeout(BOARD_TEST_TIMEOUT, async {
                loop {
                    match sub.recv().await {
                        Ok(DeviceEvent::BoardTest(report)) => return Some(report),
                        Ok(_) | Err(tokio::sync::broadcast::error::RecvError::Lagged(_)) => {
                            continue
                        }
                        Err(_) => return None,
                    }
                }
            })
            .await;
            match result {
                Ok(Some(report)) => IpcResponse::BoardTest(report),
                _ => IpcResponse::Error("The pad did not answer the board test".to_string()),
            }
        }

        IpcRequest::DetectPin {
            key_id,
            timeout_ms,
            exclude_gpio,
        } => {
            if !device.is_connected() {
                return IpcResponse::Error("Device is not connected".to_string());
            }
            let mut sub = device.subscribe();
            let effective_timeout = if timeout_ms == 0 { 10000 } else { timeout_ms };
            if let Err(_e) = device
                .send_detect_pin(key_id, effective_timeout, exclude_gpio)
                .await
            {
                return IpcResponse::PinDetected {
                    key_id,
                    gpio: 0,
                    success: false,
                };
            }
            let wait_timeout = Duration::from_millis(effective_timeout as u64 + 2000);
            let result = tokio::time::timeout(wait_timeout, async {
                loop {
                    match sub.recv().await {
                        Ok(DeviceEvent::PinDetected {
                            key_id: kid,
                            gpio,
                            success,
                        }) if kid == key_id => return Some((gpio, success)),
                        Ok(_) | Err(tokio::sync::broadcast::error::RecvError::Lagged(_)) => {
                            continue
                        }
                        Err(_) => return None,
                    }
                }
            })
            .await;

            match result {
                Ok(Some((gpio, success))) => IpcResponse::PinDetected {
                    key_id,
                    gpio,
                    success,
                },
                _ => IpcResponse::PinDetected {
                    key_id,
                    gpio: 0,
                    success: false,
                },
            }
        }

        IpcRequest::TriggerEasterEgg => {
            let _ = device
                .send_data_update(&[(67, opad_model::ui_source::SourceValue::Number(67.0))])
                .await;
            IpcResponse::EasterEggTriggered
        }
    }
}

pub async fn wait_for_layout_ack(
    events: &mut tokio::sync::broadcast::Receiver<DeviceEvent>,
    screen: Screen,
) -> IpcResponse {
    let wait = async {
        loop {
            match events.recv().await {
                Ok(DeviceEvent::LayoutAck {
                    screen: s,
                    success,
                    message,
                }) if s == screen.to_wire() => {
                    return if success {
                        IpcResponse::LayoutApplied { screen, message }
                    } else {
                        // Firmware older than a data source (e.g. the PPM
                        // ones) refuses the whole layout rather than one widget
                        let hint = if message.contains("unknown source") {
                            ". Its firmware predates that data source; update the pad's firmware to use it"
                        } else {
                            ""
                        };
                        IpcResponse::OperationRejected {
                            reason: format!("The pad rejected the layout: {}{}", message, hint),
                        }
                    };
                }
                Ok(_) | Err(tokio::sync::broadcast::error::RecvError::Lagged(_)) => continue,
                Err(_) => return IpcResponse::Error("Device event stream closed".to_string()),
            }
        }
    };
    tokio::time::timeout(Duration::from_secs(3), wait)
        .await
        .unwrap_or_else(|_| {
            IpcResponse::Error("The pad did not confirm the layout within 3s".to_string())
        })
}

/// What a request does to a flash pause the connection holds
#[derive(Debug, Clone, Copy, PartialEq, Eq)]
pub enum FlashStep {
    Prepare,
    Release,
    Other,
}

impl FlashStep {
    pub fn of(req: &IpcRequest) -> Self {
        match req {
            IpcRequest::PrepareFlash => FlashStep::Prepare,
            IpcRequest::FinishFlash | IpcRequest::ResumeDevice => FlashStep::Release,
            _ => FlashStep::Other,
        }
    }
}

/// Whether a connection holds the pad paused for a flash after this request.
/// The daemon resumes the pad itself when such a connection drops (a killed
/// or crashed `opadctl flash`), so the pad cannot stay paused until restart.
pub fn holds_flash_pause(held: bool, step: FlashStep, resp: &IpcResponse) -> bool {
    match step {
        FlashStep::Prepare => held || matches!(resp, IpcResponse::ReadyForFlash { .. }),
        FlashStep::Release => false,
        FlashStep::Other => held,
    }
}

/// The answer to anything but a Handshake on a connection that has not
/// completed one. The handshake is where a mismatched client (another IPC
/// protocol, or a GUI newer than the running daemon after an update) is
/// turned away; without this gate it could skip it, or ignore the rejection,
/// and still pause the pad or rewrite config.
pub fn refuse_before_handshake(handshaken: bool, req: &IpcRequest) -> Option<IpcResponse> {
    (!handshaken && !matches!(req, IpcRequest::Handshake { .. })).then(|| {
        IpcResponse::Error(
            "Handshake required: complete a successful Handshake before any other request"
                .to_string(),
        )
    })
}

/// Serves one IPC connection until the client leaves.
///
/// Nothing but a Handshake is served until one succeeds; a request before
/// that is refused and a rejected Handshake is answered, and in both cases
/// the connection is then closed. A pad paused for a flash by this connection
/// is resumed if the client leaves without handing it back.
pub async fn serve_connection<S: IpcTransport + ?Sized, D: DeviceLink>(
    stream: &mut S,
    state: &Arc<Mutex<DaemonState>>,
    storage: &Arc<Mutex<Option<Storage>>>,
    device: &D,
    log_hub: &LogHub,
    pending_ops: &Arc<Mutex<PendingOperations>>,
    updates: Option<&UpdateService>,
) {
    let mut handshaken = false;
    // Set while this client has the pad paused for a flash
    let mut flash_pause = false;
    while let Ok(req) = read_request(stream).await {
        if let Some(refused) = refuse_before_handshake(handshaken, &req) {
            warn!("IPC request before a successful handshake; closing the connection");
            let _ = send_response(stream, &refused).await;
            break;
        }
        let step = FlashStep::of(&req);
        let resp =
            handle_ipc_request(req, state, storage, device, log_hub, pending_ops, updates).await;
        flash_pause = holds_flash_pause(flash_pause, step, &resp);
        let rejected = matches!(resp, IpcResponse::HandshakeRejected { .. });
        handshaken |= matches!(resp, IpcResponse::HandshakeAck { .. });
        if send_response(stream, &resp).await.is_err() || rejected {
            break;
        }
    }
    if flash_pause {
        warn!(
            "The client that paused the pad for a flash disconnected without resuming it; resuming device discovery"
        );
        device.resume();
    }
}
