OPad-dev/OPad/desktop/crates/opad-storage/src/lib.rs

use chrono::Utc;
use opad_model::{
    CounterState, DeviceConfig, DeviceInfo, SwipeAction, DEFAULT_SWIPE_DOWN, DEFAULT_SWIPE_LEFT,
    DEFAULT_SWIPE_RIGHT, DEFAULT_SWIPE_UP,
};
use rusqlite::{params, Connection, OptionalExtension};
use std::path::Path;
use std::sync::atomic::{AtomicBool, Ordering};
use std::sync::Arc;
use thiserror::Error;

mod tap_stats;
pub use tap_stats::HISTORY_DAYS_KEY;

#[derive(Debug, Error)]
pub enum StorageError {
    #[error("Database error: {0}")]
    Sqlite(#[from] rusqlite::Error),
    #[error("Migration error: {0}")]
    Migration(String),
    #[error("Storage writes blocked during active gameplay/cooldown")]
    WritesBlocked,
}

pub struct Storage {
    conn: Connection,
    writes_allowed: Arc<AtomicBool>,
}

impl Storage {
    /// Opens or creates the SQLite database at the specified path and runs pending migrations.
    pub fn open<P: AsRef<Path>>(path: P) -> Result<Self, StorageError> {
        if let Some(parent) = path.as_ref().parent() {
            std::fs::create_dir_all(parent).map_err(|e| {
                StorageError::Migration(format!("Failed to create storage directory: {}", e))
            })?;
        }

        let conn = Connection::open(path)?;
        conn.execute_batch("PRAGMA journal_mode=WAL; PRAGMA foreign_keys=ON;")?;

        let storage = Self {
            conn,
            writes_allowed: Arc::new(AtomicBool::new(true)),
        };
        storage.migrate()?;
        Ok(storage)
    }

    /// Creates an in-memory database instance (primarily for tests)
    pub fn open_in_memory() -> Result<Self, StorageError> {
        let conn = Connection::open_in_memory()?;
        let storage = Self {
            conn,
            writes_allowed: Arc::new(AtomicBool::new(true)),
        };
        storage.migrate()?;
        Ok(storage)
    }

    pub fn set_writes_allowed(&self, allowed: bool) {
        self.writes_allowed.store(allowed, Ordering::SeqCst);
    }

    pub fn writes_allowed_handle(&self) -> Arc<AtomicBool> {
        self.writes_allowed.clone()
    }

    fn check_writes_allowed(&self) -> Result<(), StorageError> {
        if !self.writes_allowed.load(Ordering::SeqCst) {
            tracing::warn!("Blocked storage write while writes_allowed is false");
            return Err(StorageError::WritesBlocked);
        }
        Ok(())
    }

    fn migrate(&self) -> Result<(), StorageError> {
        self.conn.execute(
            "CREATE TABLE IF NOT EXISTS schema_migrations (
                version INTEGER PRIMARY KEY,
                applied_at TEXT NOT NULL
            );",
            [],
        )?;

        let current_version: Option<i64> = self
            .conn
            .query_row("SELECT MAX(version) FROM schema_migrations", [], |row| {
                row.get(0)
            })
            .optional()?
            .flatten();

        let v = current_version.unwrap_or(0);
        if v < 1 {
            self.apply_v1()?;
        }
        if v < 2 {
            self.apply_v2()?;
        }
        if v < 3 {
            self.apply_v3()?;
        }
        if v < 4 {
            self.apply_v4()?;
        }
        if v < 5 {
            self.apply_v5()?;
        }
        if v < 6 {
            self.apply_v6()?;
        }
        if v < 7 {
            self.apply_v7()?;
        }
        if v < 8 {
            self.apply_v8()?;
        }
        if v < 9 {
            self.apply_v9()?;
        }
        if v < 10 {
            self.apply_v10()?;
        }
        if v < 11 {
            self.apply_v11()?;
        }
        if v < 12 {
            self.apply_v12()?;
        }
        if v < 13 {
            self.apply_v13()?;
        }
        if v < 14 {
            self.apply_v14()?;
        }
        if v < 15 {
            self.apply_v15()?;
        }
        Ok(())
    }

    /// v2: configurable key press highlight color for the gameplay screen
    fn apply_v2(&self) -> Result<(), StorageError> {
        self.conn.execute_batch(
            "BEGIN TRANSACTION;
            ALTER TABLE config ADD COLUMN press_color_rgb INTEGER NOT NULL DEFAULT 16711680;
            INSERT INTO schema_migrations (version, applied_at) VALUES (2, datetime('now'));
            COMMIT;",
        )?;
        Ok(())
    }

    /// v3: custom screen layouts from the PC designer
    fn apply_v3(&self) -> Result<(), StorageError> {
        self.conn.execute_batch(
            "BEGIN TRANSACTION;
            CREATE TABLE IF NOT EXISTS layouts (
                screen INTEGER PRIMARY KEY,
                json TEXT NOT NULL,
                updated_at TEXT NOT NULL
            );
            INSERT INTO schema_migrations (version, applied_at) VALUES (3, datetime('now'));
            COMMIT;",
        )?;
        Ok(())
    }

    /// v4: update default gameplay_display_hz from 5 to 10 (§P2-7)
    fn apply_v4(&self) -> Result<(), StorageError> {
        self.conn.execute_batch(
            "BEGIN TRANSACTION;
            UPDATE config SET gameplay_display_hz = 10 WHERE gameplay_display_hz = 5;
            INSERT INTO schema_migrations (version, applied_at) VALUES (4, datetime('now'));
            COMMIT;",
        )?;
        Ok(())
    }

    /// v5: normalise legacy tosu_endpoint '/ws' to '/websocket/v2' (§P3-5)
    fn apply_v5(&self) -> Result<(), StorageError> {
        self.conn.execute_batch(
            "BEGIN TRANSACTION;
            UPDATE config SET tosu_endpoint = 'ws://127.0.0.1:24050/websocket/v2' WHERE tosu_endpoint = 'ws://127.0.0.1:24050/ws';
            INSERT INTO schema_migrations (version, applied_at) VALUES (5, datetime('now'));
            COMMIT;",
        )?;
        Ok(())
    }

    /// v6: configurable key switch GPIOs (defaults: the original fixed pins)
    fn apply_v6(&self) -> Result<(), StorageError> {
        self.conn.execute_batch(
            "BEGIN TRANSACTION;
            ALTER TABLE config ADD COLUMN key1_gpio INTEGER NOT NULL DEFAULT 14;
            ALTER TABLE config ADD COLUMN key2_gpio INTEGER NOT NULL DEFAULT 9;
            INSERT INTO schema_migrations (version, applied_at) VALUES (6, datetime('now'));
            COMMIT;",
        )?;
        Ok(())
    }

    /// v7: host-side state that is neither device config nor counters — the
    /// install identity (§W3-1) and the updaters' settings and check schedules
    /// (§U-0.4, §U-0.6). One key/value table rather than a column per setting,
    /// so adding an updater is not a migration.
    fn apply_v7(&self) -> Result<(), StorageError> {
        self.conn.execute_batch(
            "BEGIN TRANSACTION;
            CREATE TABLE IF NOT EXISTS app_state (
                key TEXT PRIMARY KEY,
                value TEXT NOT NULL,
                updated_at TEXT NOT NULL
            );
            INSERT INTO schema_migrations (version, applied_at) VALUES (7, datetime('now'));
            COMMIT;",
        )?;
        Ok(())
    }

    /// v8: update default debounce_us from 3000 to 5000 µs to eliminate switch chatter
    fn apply_v8(&self) -> Result<(), StorageError> {
        self.conn.execute_batch(
            "BEGIN TRANSACTION;
            UPDATE config SET debounce_us = 5000 WHERE debounce_us = 3000;
            INSERT INTO schema_migrations (version, applied_at) VALUES (8, datetime('now'));
            COMMIT;",
        )?;
        Ok(())
    }

    /// v12: left/right touchscreen swipe actions, as `SwipeAction` wire values
    /// (defaults: previous / next track) and their keyboard keys
    fn apply_v12(&self) -> Result<(), StorageError> {
        // Re-run safe, like v11: the columns may already be there
        let has_swipes: bool = self.conn.query_row(
            "SELECT COUNT(*) > 0 FROM pragma_table_info('config') WHERE name = 'swipe_left_action'",
            [],
            |row| row.get(0),
        )?;
        self.conn.execute_batch(&format!(
            "BEGIN TRANSACTION;
            {}
            INSERT INTO schema_migrations (version, applied_at) VALUES (12, datetime('now'));
            COMMIT;",
            if has_swipes {
                ""
            } else {
                "ALTER TABLE config ADD COLUMN swipe_left_action INTEGER NOT NULL DEFAULT 2;
                ALTER TABLE config ADD COLUMN swipe_right_action INTEGER NOT NULL DEFAULT 3;
                ALTER TABLE config ADD COLUMN swipe_left_key INTEGER NOT NULL DEFAULT 0;
                ALTER TABLE config ADD COLUMN swipe_right_key INTEGER NOT NULL DEFAULT 0;"
            }
        ))?;
        Ok(())
    }

    /// v13: up/down swipes inverted (0 = swipe up is volume up)
    fn apply_v13(&self) -> Result<(), StorageError> {
        // Re-run safe, like v11
        let has_column: bool = self.conn.query_row(
            "SELECT COUNT(*) > 0 FROM pragma_table_info('config') WHERE name = 'swipe_invert_vertical'",
            [],
            |row| row.get(0),
        )?;
        self.conn.execute_batch(&format!(
            "BEGIN TRANSACTION;
            {}
            INSERT INTO schema_migrations (version, applied_at) VALUES (13, datetime('now'));
            COMMIT;",
            if has_column {
                ""
            } else {
                "ALTER TABLE config ADD COLUMN swipe_invert_vertical INTEGER NOT NULL DEFAULT 0;"
            }
        ))?;
        Ok(())
    }

    /// v14: up/down swipe actions and keys (defaults: volume up / down). The
    /// v13 "up/down inverted" flag becomes swapped volume actions, then goes.
    fn apply_v14(&self) -> Result<(), StorageError> {
        let has_column = |name: &str| -> Result<bool, StorageError> {
            Ok(self.conn.query_row(
                "SELECT COUNT(*) > 0 FROM pragma_table_info('config') WHERE name = ?1",
                params![name],
                |row| row.get(0),
            )?)
        };
        // Re-run safe, like v11
        let add_actions = if has_column("swipe_up_action")? {
            ""
        } else {
            "ALTER TABLE config ADD COLUMN swipe_up_action INTEGER NOT NULL DEFAULT 7;
            ALTER TABLE config ADD COLUMN swipe_down_action INTEGER NOT NULL DEFAULT 8;
            ALTER TABLE config ADD COLUMN swipe_up_key INTEGER NOT NULL DEFAULT 0;
            ALTER TABLE config ADD COLUMN swipe_down_key INTEGER NOT NULL DEFAULT 0;"
        };
        let drop_invert = if has_column("swipe_invert_vertical")? {
            "UPDATE config SET swipe_up_action = 8, swipe_down_action = 7
                WHERE swipe_invert_vertical != 0;
            ALTER TABLE config DROP COLUMN swipe_invert_vertical;"
        } else {
            ""
        };
        self.conn.execute_batch(&format!(
            "BEGIN TRANSACTION;
            {add_actions}
            {drop_invert}
            INSERT INTO schema_migrations (version, applied_at) VALUES (14, datetime('now'));
            COMMIT;"
        ))?;
        Ok(())
    }

    /// v15: modifiers held with each swipe's key (osu! shortcuts like Ctrl+O)
    fn apply_v15(&self) -> Result<(), StorageError> {
        // Re-run safe, like v11
        let has_column: bool = self.conn.query_row(
            "SELECT COUNT(*) > 0 FROM pragma_table_info('config') WHERE name = 'swipe_up_modifiers'",
            [],
            |row| row.get(0),
        )?;
        self.conn.execute_batch(&format!(
            "BEGIN TRANSACTION;
            {}
            INSERT INTO schema_migrations (version, applied_at) VALUES (15, datetime('now'));
            COMMIT;",
            if has_column {
                ""
            } else {
                "ALTER TABLE config ADD COLUMN swipe_up_modifiers INTEGER NOT NULL DEFAULT 0;
                ALTER TABLE config ADD COLUMN swipe_down_modifiers INTEGER NOT NULL DEFAULT 0;
                ALTER TABLE config ADD COLUMN swipe_left_modifiers INTEGER NOT NULL DEFAULT 0;
                ALTER TABLE config ADD COLUMN swipe_right_modifiers INTEGER NOT NULL DEFAULT 0;"
            }
        ))?;
        Ok(())
    }

    /// Reads a host-side value written by [`Self::set_app_state`]
    pub fn get_app_state(&self, key: &str) -> Result<Option<String>, StorageError> {
        self.conn
            .query_row(
                "SELECT value FROM app_state WHERE key = ?1",
                params![key],
                |row| row.get::<_, String>(0),
            )
            .optional()
            .map_err(Into::into)
    }

    /// Writes a host-side value.
    ///
    /// Goes through the same P1-3 write guard as everything else: an updater
    /// recording a check time mid-map is still a storage write.
    pub fn set_app_state(&self, key: &str, value: &str) -> Result<(), StorageError> {
        self.check_writes_allowed()?;
        self.conn.execute(
            "INSERT INTO app_state (key, value, updated_at)
             VALUES (?1, ?2, datetime('now'))
             ON CONFLICT(key) DO UPDATE SET value = excluded.value, updated_at = excluded.updated_at",
            params![key, value],
        )?;
        Ok(())
    }

    /// Custom layout JSON for a screen, if one was saved
    pub fn load_layout(&self, screen: u8) -> Result<Option<String>, StorageError> {
        self.conn
            .query_row(
                "SELECT json FROM layouts WHERE screen = ?1",
                params![screen],
                |row| row.get(0),
            )
            .optional()
            .map_err(StorageError::from)
    }

    pub fn save_layout(&self, screen: u8, json: &str) -> Result<(), StorageError> {
        self.check_writes_allowed()?;
        self.conn.execute(
            "INSERT INTO layouts (screen, json, updated_at) VALUES (?1, ?2, ?3)
             ON CONFLICT(screen) DO UPDATE SET json = excluded.json, updated_at = excluded.updated_at",
            params![screen, json, Utc::now().to_rfc3339()],
        )?;
        Ok(())
    }

    pub fn delete_layout(&self, screen: u8) -> Result<(), StorageError> {
        self.check_writes_allowed()?;
        self.conn
            .execute("DELETE FROM layouts WHERE screen = ?1", params![screen])?;
        Ok(())
    }

    fn apply_v1(&self) -> Result<(), StorageError> {
        self.conn.execute_batch(
            "BEGIN TRANSACTION;

            CREATE TABLE IF NOT EXISTS device_state (
                device_id TEXT PRIMARY KEY,
                board_profile TEXT NOT NULL,
                firmware_version TEXT,
                counter_generation INTEGER NOT NULL,
                lifetime_key1 INTEGER NOT NULL,
                lifetime_key2 INTEGER NOT NULL,
                last_seen_at TEXT,
                last_sync_at TEXT
            );

            CREATE TABLE IF NOT EXISTS config (
                id INTEGER PRIMARY KEY CHECK (id = 1),
                key1_hid_usage INTEGER NOT NULL,
                key2_hid_usage INTEGER NOT NULL,
                debounce_us INTEGER NOT NULL,
                brightness INTEGER NOT NULL,
                display_sleep_seconds INTEGER NOT NULL,
                gameplay_display_hz INTEGER NOT NULL,
                tosu_endpoint TEXT NOT NULL
            );

            INSERT OR IGNORE INTO config (
                id, key1_hid_usage, key2_hid_usage, debounce_us,
                brightness, display_sleep_seconds, gameplay_display_hz, tosu_endpoint
            ) VALUES (
                1, 29, 27, 5000, 100, 600, 10, 'ws://127.0.0.1:24050/websocket/v2'
            );

            INSERT INTO schema_migrations (version, applied_at) VALUES (1, datetime('now'));

            COMMIT;",
        )?;
        Ok(())
    }

    pub fn load_config(&self) -> Result<DeviceConfig, StorageError> {
        self.conn
            .query_row(
                "SELECT key1_hid_usage, key2_hid_usage, debounce_us, brightness,
                    display_sleep_seconds, gameplay_display_hz, tosu_endpoint,
                    key1_gpio, key2_gpio, swipe_left_action, swipe_right_action,
                    swipe_left_key, swipe_right_key, swipe_up_action, swipe_down_action,
                    swipe_up_key, swipe_down_key, swipe_up_modifiers, swipe_down_modifiers,
                    swipe_left_modifiers, swipe_right_modifiers
             FROM config WHERE id = 1",
                [],
                |row| {
                    Ok(DeviceConfig {
                        key1_hid_usage: row.get(0)?,
                        key2_hid_usage: row.get(1)?,
                        debounce_us: row.get(2)?,
                        brightness: row.get(3)?,
                        display_sleep_seconds: row.get(4)?,
                        gameplay_display_hz: row.get(5)?,
                        tosu_endpoint: {
                            let ep: String = row.get(6)?;
                            if ep.trim().is_empty() {
                                "ws://127.0.0.1:24050/websocket/v2".to_string()
                            } else {
                                ep
                            }
                        },
                        key1_gpio: row.get(7)?,
                        key2_gpio: row.get(8)?,
                        swipe_left_action: SwipeAction::from_wire(row.get(9)?)
                            .unwrap_or(DEFAULT_SWIPE_LEFT),
                        swipe_right_action: SwipeAction::from_wire(row.get(10)?)
                            .unwrap_or(DEFAULT_SWIPE_RIGHT),
                        swipe_left_key: row.get(11)?,
                        swipe_right_key: row.get(12)?,
                        swipe_up_action: SwipeAction::from_wire(row.get(13)?)
                            .unwrap_or(DEFAULT_SWIPE_UP),
                        swipe_down_action: SwipeAction::from_wire(row.get(14)?)
                            .unwrap_or(DEFAULT_SWIPE_DOWN),
                        swipe_up_key: row.get(15)?,
                        swipe_down_key: row.get(16)?,
                        swipe_up_modifiers: row.get(17)?,
                        swipe_down_modifiers: row.get(18)?,
                        swipe_left_modifiers: row.get(19)?,
                        swipe_right_modifiers: row.get(20)?,
                    })
                },
            )
            .map_err(StorageError::from)
    }

    pub fn save_config(&self, config: &DeviceConfig) -> Result<(), StorageError> {
        self.check_writes_allowed()?;
        self.conn.execute(
            "UPDATE config SET
                key1_hid_usage = ?1,
                key2_hid_usage = ?2,
                debounce_us = ?3,
                brightness = ?4,
                display_sleep_seconds = ?5,
                gameplay_display_hz = ?6,
                tosu_endpoint = ?7,
                key1_gpio = ?8,
                key2_gpio = ?9,
                swipe_left_action = ?10,
                swipe_right_action = ?11,
                swipe_left_key = ?12,
                swipe_right_key = ?13,
                swipe_up_action = ?14,
                swipe_down_action = ?15,
                swipe_up_key = ?16,
                swipe_down_key = ?17,
                swipe_up_modifiers = ?18,
                swipe_down_modifiers = ?19,
                swipe_left_modifiers = ?20,
                swipe_right_modifiers = ?21
             WHERE id = 1",
            params![
                config.key1_hid_usage,
                config.key2_hid_usage,
                config.debounce_us,
                config.brightness,
                config.display_sleep_seconds,
                config.gameplay_display_hz,
                config.tosu_endpoint,
                config.key1_gpio,
                config.key2_gpio,
                config.swipe_left_action.to_wire(),
                config.swipe_right_action.to_wire(),
                config.swipe_left_key,
                config.swipe_right_key,
                config.swipe_up_action.to_wire(),
                config.swipe_down_action.to_wire(),
                config.swipe_up_key,
                config.swipe_down_key,
                config.swipe_up_modifiers,
                config.swipe_down_modifiers,
                config.swipe_left_modifiers,
                config.swipe_right_modifiers,
            ],
        )?;
        Ok(())
    }

    pub fn load_device_state(&self, device_id: &str) -> Result<Option<CounterState>, StorageError> {
        self.conn
            .query_row(
                "SELECT device_id, counter_generation, lifetime_key1, lifetime_key2
                 FROM device_state WHERE device_id = ?1",
                params![device_id],
                |row| {
                    let k1: i64 = row.get(2)?;
                    let k2: i64 = row.get(3)?;
                    Ok(CounterState {
                        device_id: row.get(0)?,
                        counter_generation: row.get(1)?,
                        lifetime_key1: k1 as u64,
                        lifetime_key2: k2 as u64,
                        map_key1: 0,
                        map_key2: 0,
                    })
                },
            )
            .optional()
            .map_err(StorageError::from)
    }

    pub fn list_device_states(&self) -> Result<Vec<(DeviceInfo, CounterState)>, StorageError> {
        let mut stmt = self.conn.prepare(
            "SELECT device_id, board_profile, firmware_version, counter_generation,
                    lifetime_key1, lifetime_key2, last_seen_at, last_sync_at
             FROM device_state ORDER BY last_seen_at DESC",
        )?;
        let rows = stmt.query_map([], |row| {
            let device_id: String = row.get(0)?;
            let board_profile: String = row.get(1)?;
            let firmware_version: Option<String> = row.get(2)?;
            let counter_generation: u32 = row.get(3)?;
            let lifetime_key1: i64 = row.get(4)?;
            let lifetime_key2: i64 = row.get(5)?;

            let info = DeviceInfo {
                device_id: device_id.clone(),
                board_profile,
                firmware_version: firmware_version.unwrap_or_default(),
                protocol_version: 1,
                running_partition: None,
            };
            let counters = CounterState {
                device_id,
                counter_generation,
                lifetime_key1: lifetime_key1 as u64,
                lifetime_key2: lifetime_key2 as u64,
                map_key1: 0,
                map_key2: 0,
            };
            Ok((info, counters))
        })?;

        let mut list = Vec::new();
        for item in rows {
            list.push(item?);
        }
        Ok(list)
    }

    pub fn load_latest_device_state(
        &self,
    ) -> Result<Option<(DeviceInfo, CounterState)>, StorageError> {
        let states = self.list_device_states()?;
        Ok(states.into_iter().next())
    }

    pub fn touch_device_last_seen(&self, device_id: &str) -> Result<(), StorageError> {
        self.check_writes_allowed()?;
        let now = Utc::now().to_rfc3339();
        self.conn.execute(
            "UPDATE device_state SET last_seen_at = ?1 WHERE device_id = ?2",
            params![now, device_id],
        )?;
        Ok(())
    }

    pub fn save_device_state(
        &self,
        info: &DeviceInfo,
        counters: &CounterState,
    ) -> Result<(), StorageError> {
        self.check_writes_allowed()?;
        let now = Utc::now().to_rfc3339();
        self.conn.execute(
            "INSERT INTO device_state (
                device_id, board_profile, firmware_version, counter_generation,
                lifetime_key1, lifetime_key2, last_seen_at, last_sync_at
            ) VALUES (?1, ?2, ?3, ?4, ?5, ?6, ?7, ?7)
            ON CONFLICT(device_id) DO UPDATE SET
                board_profile = excluded.board_profile,
                firmware_version = excluded.firmware_version,
                counter_generation = excluded.counter_generation,
                lifetime_key1 = excluded.lifetime_key1,
                lifetime_key2 = excluded.lifetime_key2,
                last_seen_at = excluded.last_seen_at,
                last_sync_at = excluded.last_sync_at",
            params![
                info.device_id,
                info.board_profile,
                info.firmware_version,
                counters.counter_generation,
                counters.lifetime_key1 as i64,
                counters.lifetime_key2 as i64,
                now,
            ],
        )?;
        Ok(())
    }
}

/// Counter reconciliation algorithm (§13):
/// 1. If generations differ, the newer generation takes precedence.
/// 2. For identical generation, take the maximum valid value for each physical key.
pub fn reconcile_counters(pc: &CounterState, esp: &CounterState) -> CounterState {
    if pc.device_id != esp.device_id && !pc.device_id.is_empty() && !esp.device_id.is_empty() {
        tracing::warn!(
            "Reconciling counters with mismatched device IDs (PC: {}, ESP: {})",
            pc.device_id,
            esp.device_id
        );
    }

    if pc.counter_generation > esp.counter_generation {
        // PC has newer generation (e.g. deliberate reset or imported backup)
        pc.clone()
    } else if esp.counter_generation > pc.counter_generation {
        // ESP has newer generation
        esp.clone()
    } else {
        // Identical generation: maximum valid lifetime counters win
        CounterState {
            device_id: if !pc.device_id.is_empty() {
                pc.device_id.clone()
            } else {
                esp.device_id.clone()
            },
            counter_generation: pc.counter_generation,
            lifetime_key1: pc.lifetime_key1.max(esp.lifetime_key1),
            lifetime_key2: pc.lifetime_key2.max(esp.lifetime_key2),
            map_key1: esp.map_key1,
            map_key2: esp.map_key2,
        }
    }
}
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
